konih/atmosmesh/docs/design/atmosmesh-gift.md

# AtmosMesh Gift — design and architecture proposal

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

## 1. What is being built, and the constraint that defines it

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

### The giftability contract

| # | Rule | Consequence |
| --- | --- | --- |
| G1 | The recipient never sees a terminal | Wi-Fi, location and units are set on-screen |
| G2 | No account, no API key, no subscription | Open-Meteo (keyless) for outdoor data; never OpenWeatherMap |
| G3 | It is silent | No fan. This disqualifies every PM sensor with a fan — see §5 |
| G4 | It is useful with no network at all | Onboard sensors render offline; the network adds outdoor data, clock and optional MQTT |
| G5 | It never lies about a number | An estimate may be shown, and must be labelled as one: only a real NDIR-class part may carry a bare `CO₂` label (D-002, `inventory.md:415`). A stale reading is never a zero |
| G6 | It is recoverable without tools | On-screen "forget network"; a fallback setup access point |

## 2. Reference survey

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

**Nothing from these repos gets imported.** They are read; AtmosMesh code is written.

## 3. The board, and what it actually allows

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

### Pin map (community reference — a hypothesis to verify at bring-up, not a datasheet)

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

### The free-pin budget — the single most important fact

**Three pins, one of them input-only.**

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

> **Every sensor on this product must be I²C, and they all share one bus on CN1.**

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

### Power

The CYD's 3.3 V LDO has little headroom once the panel and backlight are lit (`inventory.md:584`),
so the sensor choice in §5 is partly a power decision. **With the chosen set — ENS160 + AHT20 and
BME280 — this is not expected to be a problem:** the BME280 is a microamp part, and while the
ENS160 drives a metal-oxide hotplate and is therefore not one, it is nowhere near the 205 mA pulse
of the CO₂ sensor this design rejected. **Take the ENS160's actual figure from its datasheet and
then measure it at GF-02** — this repo does not take heater currents from memory
(`inventory.md:415`), and "not expected to be a problem" is a hypothesis until the rail is watched.

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

### Errata to design around

- **Display controller unknown.** `2432S028` ships with ILI9341 *or* ST7789, differing in colour
  inversion and RGB/BGR order. The community heuristic is that **dual-USB boards (Micro-B + Type-C)
  are the ST7789 "CYD2USB" variant with inverted colours** — and the inventory records the operator's
  units as having *both* connectors (`inventory.md:567`). **Working hypothesis: these are ST7789,
  colour-inverted.** Unverified. §6 makes this a runtime concern rather than a rebuild.
- **Never connect both USB ports at once** — one bridge, two sockets.
- Some Type-C sockets on this board lack CC resistors and will not enumerate with a C-to-C cable.
- Touch shares no bus with the TFT; use the bit-banged XPT2046 driver to avoid contention.
- **4 MB flash.** An Arduino + LVGL + Wi-Fi image is comfortably under 2 MB, so a dual-OTA partition
  layout fits — but only just, and it must be decided before the first flash, not after.

## 4. Honest objections to the premise

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

## 5. Sensors

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

### The build — €0, both parts already free in the drawer

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

**Two things about the ENS160 that must be handled, not assumed:**

- **It needs warm-up.** ScioSense state roughly **3 minutes** before readings are meaningful, plus
  a longer first-use conditioning period. That is precisely what §8's `WARMING_UP` state exists
  for: on a gift's first power-on the screen must say "Warming up…" and show `"--"`, not a wrong
  number that later moves. Take the exact conditioning figure from the datasheet at GF-02 — this
  repo does not take heater or warm-up numbers from memory (`inventory.md:415`).
- **Its current is a hotplate current, not a microamp one.** It will not trouble the 3.3 V rail the
  way the SCD41's 205 mA pulse would, but the figure goes in `inventory.md` measured, not guessed.
  The module carries a regulator for the ENS160's 1.8 V core; **feed it 3V3** until that regulator
  and the board's pull-ups have been inspected.

### The eCO₂ register: displayed, but never labelled bare "CO₂"

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

**Why that is good enough here.** In a home the dominant source of both VOC bio-effluents and CO₂
is the same thing — people. They co-vary, which is why ScioSense's own Figure 3 shows `eCO₂`
tracking a reference NDIR sensor closely across two meeting sessions, and why their Figure 4 argues
`eCO₂` is *better* than NDIR in a bedroom or bathroom, because it also catches odours and
bio-effluents a pure CO₂ sensor is blind to. Driving a ventilation prompt from it is the sensor's
designed purpose, not an abuse of it. **So the Gift shows a stuffiness reading and does say "open a
window."**

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

That second case is why the **label** matters even though the **signal** is useful.

### The one hard rule on this part

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

**`gift_view_model` carries the host test** — asserting that the eCO₂ value always reaches the UI
and MQTT through its estimated-label path, and that no code path emits it under a bare CO₂ name or
entity id. The test now guards the label rather than suppressing the value.

### Still free in stock, if a later revision wants better

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

### If CO₂ is wanted after all, the cheap way in

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

### Deliberately excluded, with reasons

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

### If particulates are non-negotiable

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

## 6. Firmware architecture

AtmosMesh Gift becomes a fourth product under ADR-0001's existing four-layer scheme — one
PlatformIO project, one explicit composition root, shared host-tested domain code.

```text
firmware/
  include/atmosmesh/
    gift_pins.hpp            CYD pin map + CN1 I2C assignment, one place
    gift_profile.hpp         ProductProfile entry: atmosmesh-gift-v1
    air_band.hpp             TVOC / AQI -> named band + verdict wording [host-tested]
    reading_state.hpp        WARMING_UP | OK | STALE | FAULT            [host-tested]
    wifi_credentials.hpp     SSID/PSK validation, NVS record shape      [host-tested]
    provisioning.hpp         the provisioning state machine             [host-tested]
    gift_view_model.hpp      every string the UI draws, incl. "--"      [host-tested]
    gift_openmeteo.hpp       JSON -> outdoor reading struct             [host-tested]
    gift_mqtt_contract.hpp   GiftMqttState, extends the D-007 contract  [host-tested]
  src/
    air_band.cpp  reading_state.cpp  wifi_credentials.cpp
    provisioning.cpp  gift_view_model.cpp  gift_openmeteo.cpp     <- native env
    gift_display.cpp      LovyanGFX panel + LVGL bind      \
    gift_touch.cpp        XPT2046, bit-banged               |
    gift_sensors.cpp      ENS160+AHT20 + BME280, one bus   |  device only,
    gift_nvs_store.cpp    Preferences/NVS                   |  excluded from
    gift_net.cpp          Wi-Fi + NTP + Open-Meteo client   |  the native env
    gift_ui_*.cpp         one file per screen              /
    products/atmosmesh_gift_v1.cpp   the composition root
```

**The rule that makes this testable:** anything that decides *what* to show is a pure function in
the native env with Unity tests written first (AGENTS.md workflow step 3, GUIDELINES §A3). Anything
that touches a pin or a socket is a thin device-only file with no logic in it. `gift_view_model`
is the seam — it turns readings and state into the exact strings and colour-band enums the LVGL
layer paints, so the screen's behaviour on a dead sensor is a host test, not a bench observation.

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

**MQTT stays exactly as D-007 and D-019 define it,** and ships **disabled**. A gift recipient with
no broker must never see an error about one. Settings gains an "Advanced → Home Assistant" panel
that, when filled in, brings up the existing `mqtt_session` machinery with a `GiftMqttState` built
from the same `MqttReading{value, valid, age_ms}` shape the other products use — so a stopped
sensor reaches Home Assistant as *unavailable*, never as clean air.

## 7. Wi-Fi provisioning

Structurally Heftie's, with its two weaknesses fixed and one thing neither reference does.

```text
         ┌──────────────┐
  boot ─►│  LOAD_CREDS  │
         └──────┬───────┘
         none   │   found
      ┌─────────┴─────────┐
      ▼                   ▼
┌───────────┐      ┌─────────────┐  ok   ┌────────┐
│  WIZARD   │      │ CONNECTING  ├──────►│ ONLINE │
│ scan list │      └──────┬──────┘       └───┬────┘
│  keyboard │   timeout/  │                  │ link lost
└─────┬─────┘   auth fail │                  ▼
      │                   ▼            ┌───────────┐
      │            ┌─────────────┐     │ RETRYING  │
      │            │   FAILED    │     │ backoff   │
      │            │ reason shown│     └───────────┘
      │            └──────┬──────┘
      │                   │ 3 failures, or user taps "Set up with my phone"
      ▼                   ▼
   ┌────────────────────────────────┐
   │ SETUP_AP  SoftAP + captive     │
   │ portal + join QR on the screen │
   └────────────────────────────────┘
```

Decisions inside it:

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

## 8. The interface

240×320 panel, **landscape 320×240** on a stand. Designed for *pressed taps on large targets*,
because §4.2 says the touch is resistive.

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

```text
┌────────────────────────────────────────────┐
│  Living room            ⌂ 21:04    [ wifi ]│
│                                            │
│        ╭──────────╮                        │
│        │  Stuffy  │      21.4 °C           │
│        │          │      47 % RH           │
│        ╰──────────╯                        │
│        Air quality      eCO₂ ~1240 est.    │
│                         TVOC  340 ppb      │
│      Open a window                         │
├────────────────────────────────────────────┤
│   Now  │  Trend  │  Outside  │  Settings   │
└────────────────────────────────────────────┘
```

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

**States are part of the design, not an afterthought (G5):**

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

## 9. Open decisions for the operator

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

1. **Product name.** `Gift` fits the existing one-word-noun family (Room, Spot, Aqua, Grove) and
   states the intent. Alternatives: `Glass`, `Desk`, `Cube`. *Recommended: Gift.*
2. ~~**Sensor tier.**~~ **Answered 2026-09-20 → D-036: ENS160 + AHT20 for gas, BME280 for
   climate, SHT41 kept as the fleet spare, no CO₂ sensor.** See §5. The MH-Z19C upgrade path stays
   open and GPIO35 is reserved for it.
3. **Which CYD.** Use an on-hand `R` (resistive, stylus) unit, or buy a `C` (capacitive) unit for
   the gift and keep the `R` pair for bench work. *Recommended: buy a `C` — see §4.2.*
4. **Graphics stack.** LVGL 9 + LovyanGFX with runtime panel detection, or LVGL 8 + TFT_eSPI to
   stay closer to nicholaswilde's copyable UI code. *Recommended: LVGL 9 + LovyanGFX — see §6.*
5. **Does MQTT ship enabled?** *Recommended: no — off by default, enabled in Settings.*
6. **Enclosure.** Not cosmetic: §4.1 makes sensor placement a measurement decision. A printed case
   that holds the sensors on the pigtail away from the board, with its own vents, or no case.
7. **OTA.** A dual-OTA partition layout on 4 MB must be chosen before the first flash. Worth it for
   a device that leaves the house; costs the option of a single large app partition.

## 10. Proposed story sequence

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

| Story | Outcome | Gate |
| --- | --- | --- |
| GF-01 | CYD unit identified from its own silicon: display controller, touch controller, board suffix, RGB LED and LDR exercised | A self-test image reports every device over serial and on screen |
| GF-02 | CN1 I²C bus proven with one sensor, pull-ups measured, 3.3 V rail watched under load | Meter (or scope) evidence on the rail; `inventory.md` updated with measured facts, replacing the community pin map with probed ones |
| GF-03 | Host-tested domain: `air_band`, `reading_state`, `wifi_credentials`, `provisioning`, `gift_view_model` | `task test` green, tests written first |
| GF-04 | LVGL 9 + LovyanGFX bring-up with runtime panel detection; the Now screen renders from fake readings | Both on-hand units render correctly from one image |
| GF-05 | Provisioning end to end: wizard, keyboard, test-before-save, inline failure, SetupAP + join QR, forget | A factory-reset unit joins a network with no serial cable touched |
| GF-06 | ENS160+AHT20 and BME280 live, four reading states visible on demand, `eCO2` shown as an estimate | Sensor unplugged mid-run shows FAULT not a frozen number; a host test proves every `eCO2` path carries the estimated label and none emits a bare `co2` name or entity id |
| GF-07 | Open-Meteo: geocoding search, forecast, outdoor AQI, NTP clock | Works with no account and no key |
| GF-08 | Optional MQTT + Home Assistant discovery, off by default | Existing D-007 contract unchanged |
| GF-09 | Enclosure, self-heating measured against a reference thermometer, offset documented or designed out | §4.1 closed with numbers |
| GF-10 | 48-hour unattended run, then hand it over | Power-loss, sensor-loss and network-loss behaviour all observed |
