konih/atmosmesh/agent-context/stories/SP-01.md

# SP-01 — AtmosMesh Spot: a 3.3 V presence-and-climate node on an ESP32-C3 SuperMini

- **Status:** Proposed (design spec; carrier soldering started 4 September 2026)
- **Priority:** P3 — small, self-contained, and the ESP32-C3 toolchain spike R2-01 needs anyway
- **Milestone:** Spot v1
- **Depends on:** nothing open. SuperMini pin map and OLED bus pins are photo- and
  scan-verified, the LD2410S datasheet is read, the SHT41 and VEML7700 breakouts are photographed
  (see Evidence).
- **First unit:** SHT41 + VEML7700 + HLK-LD2410S on the board and the DS18B20 probe on a
  terminal. **No BME280** (operator decision, 5 September 2026; the outdoor-cable variant that
  existed on 4 September is withdrawn). Drawings and bill of materials in
  [`hardware/kicad/atmosmesh-spot/wiring.md`](../../hardware/kicad/atmosmesh-spot/wiring.md).

## User story

As the operator, I want a palm-sized station that I can build in an evening, put in any room that
has a USB socket, and read on its own little screen or in Home Assistant, so that the rooms without
a Room-class station get temperature, humidity, light and — the thing PIR never gave me — whether
somebody is actually in the room; and I want a temperature probe on a lead so the same node can
watch a radiator, a window pane or the air outside a window without any electronics leaving the
room.

## Outcome

One carrier on a 14 × 20 hole perfboard, one population:

| Product id | On the board | On a terminal | Bus |
| --- | --- | --- | --- |
| `atmosmesh-spot` | SuperMini, SHT41 at `0x44`, VEML7700 at `0x10`, HLK-LD2410S radar | DS18B20 probe, 2.5 m, 1-Wire | one 3.3 V I²C bus at 100 kHz, OLED at `0x3C` |

Everything is one 3.3 V domain. Firmware is one product built with a PlatformIO `esp32-c3`
environment, publishing on the existing MQTT contract, with the on-board 72 × 40 OLED cycling
through the values.

**The first unit takes the last SHT41 spare and the only LD2410S.** After Room, Room v2 and
this unit, one SHT41 and one VEML7700 remain; a second Spot needs another SHT41 bought and a
second radar, or goes without presence. The six BME280 in stock stay unassigned.

## Sensor choices, and why

- **SHT41 for temperature and humidity.** The accurate one (about ±1.8 %RH, ±0.2 °C), and the
  last free spare.
- **No BME280.** Decided against on 5 September. It would have brought pressure and, on a cable,
  an outdoor reading; the operator prefers a simpler board without the cable, its series
  resistors, its clamps and its terminal. Pressure is not a Spot value; an outdoor temperature,
  if wanted, comes from the DS18B20 probe held out of the window.
- **VEML7700** for lux, as on Room. Mounted on its header facing the room, on the side away from
  the OLED so the display's own glow does not become the reading.
- **HLK-LD2410S** for presence. It is the 3.3 V, low-power member of the LD24xx family with a
  presence output pin and a UART, which is exactly what a board without a 5 V domain needs.
  There is one, and it was reserved for Room v2; Room v2 has a 5 V domain and takes the LD2450
  instead (R2-01 updated). The manual (read 4 September, filed under
  `docs/hardware/datasheets/`) settles it: 3.0–3.6 V supply, every pin 0–3.3 V, average current
  under 1 mA with transmit peaks near 118 mA, presence on pin `OT2` (high = occupied), UART on
  `OT1` (TX) and `RX` at 115200 8N1.
- **DS18B20 probe** because 1-Wire is built for a lead and the probe is already encapsulated.
  It is the only thing that may leave the room.
- **Not potted, not outside.** Coating the ceramic antenna detunes the SuperMini's weakest part.
- **Soil header dropped.** Three sensors and a radar fill the small board; a plant node is a
  different population and can be a later story.

## Controller: ESP32-C3 SuperMini OLED — verified

- 3.3 V logic and a small on-board LDO from USB 5 V. **The `5V` pin is never wired to anything on
  the carrier.**
- OLED: SSD1306 driving a 72 × 40 panel with a column offset; some libraries name the same panel
  "70 × 42". **Scanned 4 September: `0x3C` on SDA = GPIO5, SCL = GPIO6**, nothing else on the bus
  of the bare module. Whether the OLED has its own pull-ups is a meter reading still to take.
- Strapping pins **GPIO2, GPIO8, GPIO9** stay unused as inputs. GPIO8 drives the on-board LED,
  GPIO9 is the BOOT button — the display page button in firmware, nothing on the carrier.
- **Pin map, photo-verified 4 September** (USB on the left, OLED up). Row A, the side with the
  `PWR` and `IO8` LEDs, from the USB end: `5V GD 3V RX TX 2 1 0`. Row B, from the USB end:
  `10 9 8 7 6 5 4 3`. `RX`/`TX` are GPIO20/21. This is not the plain SuperMini's map.
- GPIO assignment: GPIO5/6 I²C (row B); **GPIO3** radar `OT2` (presence, row B far end);
  the board's marked **`RX` (GPIO20)** ← radar `OT1` (its TX) and **`TX` (GPIO21)** → radar
  `RX`, i.e. UART0, `Serial0` in the Arduino core (row A); **GPIO4** 1-Wire (row B). GPIO0 and
  GPIO1, two of the five ADC pins, stay free. Changed 5 September on the operator's question:
  the earlier choice of GPIO0/1 as a second UART avoided the ROM boot log that the C3 prints on
  `TX` at every reset, but that log cannot form a radar command (header `FD FC FB FA` plus a
  valid length), the USB console is native USB on this board so UART0 is otherwise unused, and
  the labelled pins are the ones a builder reaches for.
- Known SuperMini trait: the ceramic antenna couples badly and Wi-Fi drops at full TX power.
  Firmware limits TX power to about 8.5 dBm at start-up as part of the product.
- Pin rows: 8 pins each, **7 pitches (17.78 mm) apart — dry-fit confirmed by the operator on
  4 September**: pushed into the 14 × 20 board the module fits with three free columns on each
  side, i.e. rows at columns 4 and 11.
- Chip on the first unit: ESP32-C3 rev 4, 4 MB flash, MAC `E4:EC:E6:92:05:D4`.

## Sensor set, bus map and headers

| Device | Address / pin | Header | Notes |
| --- | --- | --- | --- |
| SHT41 | `0x44` | `J_SHT` 4-pin: VIN, GND, SCL, SDA | Photo-confirmed order. The `SHT4X` board carries a 662K LDO, a level shifter and a fitted `103` array on the sensor side; its host-side pull-up pads are empty, so it adds **no** pull-up to the bus |
| VEML7700 | `0x10` | `J_VEML` 5-pin: VIN, 3VO (NC), GND, SCL, SDA | Photo-confirmed order (`HW-900`); same LDO-plus-shifter architecture with all four array elements in use, so about 10 kΩ per line; `3VO` never wired |
| HLK-LD2410S | `OT2` → GPIO3, `OT1` → `RX` (GPIO20), `RX` ← `TX` (GPIO21) | `J_RAD` 5-pin in the manual's J2 order: **3V3, GND, OT1, RX, OT2** | Datasheet- and photo-confirmed 3.3 V part. `OT2` is the presence output (high = occupied), direct to GPIO3. `OT1` is the UART **TX** despite the name. `C_RAD_BULK` 100 µF at the header for the ~118 mA transmit peaks |
| OLED on the SuperMini | `0x3C` | on board | Scan-confirmed on GPIO5/6 |
| DS18B20 probe | 1-Wire, GPIO4 | `J_1W` 3-pole terminal: 3V3, DQ, GND with `R_1W` 4.7 kΩ to 3V3 | Surface, water or outside-the-window temperature on the 2.5 m lead |

No address collides. Carrier pull-ups `R_PU_SDA`/`R_PU_SCL` are **4.7 kΩ**; with the VEML7700's
10 kΩ the line sees about 3.2 kΩ, with an assumed 10 kΩ on the OLED about 2.4 kΩ — 1.4 mA sink,
well inside the 3 mA limit. Bus speed 100 kHz; the bus never leaves the board.

Radar placement rules, from Room v2's lesson in reverse: the antenna face looks into the room
with no metal or copper in front of it, the module stands on its header at the board edge, and it
must not look across a fan, a curtain in a draught or a pet's bed — a 24 GHz radar reports every
one of those as a moving target. Presence is confirmed with a person sitting still and with the
room empty before it drives anything.

## Board layout — 14 × 20 holes (35.6 × 50.8 mm)

Columns 1–14 left to right, rows 1–20 top to bottom, viewed from the component side, USB
overhanging the row-1 edge. The 10 × 24 board does not fit: with the rows 7 pitches apart the
module needs 8 of the 10 columns and leaves no keep-out beside the antenna end.

**The authoritative hole-by-hole drawing is in
[`hardware/kicad/atmosmesh-spot/wiring.md`](../../hardware/kicad/atmosmesh-spot/wiring.md)
(section 3) and its SVGs.** In outline:

| Rows | Contents |
| --- | --- |
| 3–10 | `U1` socket rows at columns 4 (row A: `5V GD 3V RX TX 2 1 0`) and 11 (row B: `10 9 8 7 6 5 4 3`), 7 pitches apart |
| 9–13 | keep-out around the module's far end: buttons and antenna. No copper, no wire, no coating |
| 14 | `R_PU_SDA`, `R_PU_SCL` 4.7 kΩ, `C1` |
| 15 | `J_SHT` (cols 1–4), `J_VEML` (cols 7–11), both modules standing upright |
| 16–18 | decoupling, test points, `R_1W`, `C_RAD_BULK`/`C_RAD` |
| 20 | `J_RAD` (cols 1–5, radar upright, face outward), `J_1W` terminal (cols 8/10/12) |

`J_VEML` and `J_RAD` sit on different edges so the light sensor can face one way and the radar
the other; on a windowsill unit the radar faces the room and the VEML7700 faces up.

Wiring by pin name, all on one 3.3 V rail:

```text
U1 3V3 ──┬── J_SHT VIN  ──┤C_SHT 100n── GND
         ├── J_VEML VIN ──┤C_VEML 100n── GND          J_VEML 3VO: not connected
         ├── J_RAD 3V3  ──┬┤C_RAD_BULK 100µ (+)── GND
         │                └┤C_RAD 100n── GND
         ├── J_1W 3V3 ── R_1W 4k7 ── J_1W DQ ── U1 GPIO4
         ├── C1 100n ── GND
         └── R_PU_SDA 4k7 ── SDA      R_PU_SCL 4k7 ── SCL

U1 GPIO5 (SDA) ── SDA ── J_SHT SDA ── J_VEML SDA
U1 GPIO6 (SCL) ── SCL ── J_SHT SCL ── J_VEML SCL
J_RAD OT2 ── U1 GPIO3           presence, high = occupied, 3.3 V logic, direct
J_RAD OT1 ── U1 RX (GPIO20)     radar UART TX → frames in (C3 UART0 RX, Serial0)
J_RAD RX  ── U1 TX (GPIO21)     configuration out (C3 UART0 TX)
U1 GND ── ground rail ── every GND
U1 5V  ── nothing
```

## Power

USB only. The SHT41 and VEML7700 draw about a milliampere each, the OLED a few. The radar's
transmit bursts are why `C_RAD_BULK` sits at its header. The other real load is the C3's Wi-Fi
transmit burst (up to ~350 mA) on the SuperMini's small LDO, which is why the TX-power limit
matters for supply as well as for range. If the board browns out on connect, add 10 µF at
`TP_3V3` and record it.

## Firmware

**Built and flashed 5 September 2026 — see [SP-02](SP-02.md) for the image and its evidence.**

- Composition root `firmware/src/products/atmosmesh_spot_v1.cpp` per ADR-0001, PlatformIO
  environment `atmosmesh-spot-v1` for the C3 (USB CDC on boot). The product repeats the hello
  with its name and station id.
- Reuses the I²C scan-and-report behaviour and the MQTT contract shape (`{value, unit, valid,
  age_ms}`). Station id `atmosmesh-spot-0001`, following the product pattern already in use
  (`atmosmesh-room-0001`), one per unit.
- Entities: `temperature_c`, `humidity_pct` (SHT41), `illuminance_lx`, `presence` (radar `OT2`
  through a debounce and hold), `probe_temperature_c` (DS18B20, unavailable when no probe
  answers), `presence_distance_cm` and `presence_state` from the LD2410S UART (minimal frame
  `6E · state · distance · 62`, standard frame also decoded), `wifi_rssi_dbm`. The product works
  on `OT2` alone; the UART entities stay unavailable until frames arrive.
- OLED: one value per page, rotated every 3 s, the BOOT button forces the next one; a presence
  glyph top-right and the link state bottom-right on every page.
- Bus speed 100 kHz. Wi-Fi TX power limited to 8.5 dBm at start-up; RSSI in every 5 s log line
  and published.

## In scope

- One carrier; the first build goes on the bench next to Room for the comparison criteria.
- PlatformIO C3 product environment, host-tested Sensirion CRC, MQTT discovery for the new
  product, 1-Wire probe reading.

## Out of scope

- Battery operation. The SuperMini has no charger, and deep-sleep with an OLED and a radar is a
  different product.
- Any electronics outside besides the probe. Coating or potting the node is rejected above.
- A BME280, on the board or on a cable (withdrawn 5 September).
- The ESP32-C6 modules. Same spike, different chip; after the C3 works.
- Any 5 V sensor, including the LD2450. The board has no 5 V domain by design.
- Radar zones, distance thresholds and multi-target anything.

## Acceptance criteria

- [x] Given the PlatformIO C3 environment, when a firmware builds and flashes, then the serial
      log shows a hello and a bus scan on real hardware. **Met on 4 September by
      `firmware/tools/c3scan`** and on 5 September by the product image itself
      (`spot: boot product=atmosmesh-spot-v1 station=atmosmesh-spot-0001 …`, SP-02).
- [x] Given the SuperMini photographed and scanned, when the OLED pins and the breakout pull-ups
      are recorded in `docs/hardware/inventory.md`, then the carrier's `R_PU_*` value is written
      down. **4.7 kΩ**; only the OLED's own pull-up is still a meter reading.
- [x] Given the LD2410S datasheet, when supply voltage, current and output level are recorded,
      then the radar header is either approved for 3.3 V or the radar is struck from this story.
      **Approved:** 3.0–3.6 V, all pins 0–3.3 V (`docs/hardware/datasheets/README.md`).
- [x] Given the bus scanned with only the OLED fitted, then exactly `0x3C` answers; with the
      sensors fitted, `0x44` and `0x10` join it and nothing else. **Bare module 4 September:
      `0x3C` only. Soldered carrier 5 September: `0x10 0x3C 0x44`, nothing else.**
- [ ] Given the node beside Room's SHT41 for one hour, when the readings are compared, then
      temperature agrees within 0.5 °C and humidity within 3 %RH, or the difference is explained.
- [ ] Given a person sitting still for 5 minutes, then `presence` stays `on`; given the room
      empty for 5 minutes with any fan or curtain in the radar's view noted, it is `off`.
- [ ] Given the probe rung out and connected, then `temperature_probe` tracks a hand and agrees
      with the SHT41 within 1 °C in still room air.
- [ ] Given Wi-Fi at limited TX power, when the node runs for 24 hours, then no reconnect gap
      longer than 5 minutes appears in the log.
- [ ] Given the probe unplugged at runtime, then the other entities keep updating and
      `temperature_probe` reports unavailable within one publish interval.

## Validation

- Automated: Sensirion CRC against datasheet examples; MQTT payload schema; unavailable-device
  behaviour for each sensor independently; presence hold-time logic.
- Manual: bus scans per stage, radar `OT2` idle and active levels with the meter before GPIO3 is
  connected, side-by-side comparison with Room, presence still-sitting and empty-room tests,
  RSSI log.
- Failure/edge case: any breakout unplugged at runtime; USB power cycled (reconnects without
  manual reset); radar `OT2` stuck high; probe lead shorted DQ to GND (the 4.7 kΩ limits it and
  the bus recovers when the short clears).

## Evidence

- 2026-09-04 — HLK-LD2410S user manual V1.3 and serial protocol V1.00 retrieved from Hi-Link's
  official Drive folder into `docs/hardware/datasheets/` (SHA-256 in that README). Table 3-2:
  J2 = `3V3` (3.0–3.6 V), `GND`, `OT1` UART_TX, `RX` UART_RX, `OT2` presence IO, all 0–3.3 V.
  Table 2-1: average current 0.04–0.6 mA; page-4 tool screenshots show peaks near 118 mA.
  Protocol section 2: 115200 8N1, minimal frame `6E · state · distance(2) · 62`.
- 2026-09-04 — operator read the breakouts: VEML7700 carries a `103` part, SHT41 has an empty
  `103` footprint. Meter confirmation of ~10 kΩ from SDA and SCL to VIN on the VEML7700 still to do.
- 2026-09-04 22:42–22:44 — nine photos (SuperMini on the perfboard, SHT41 front/back, LD2410S
  front/back, VEML7700 front/back, BME280 front/back), evaluated and deleted afterwards at the
  operator's request. Facts recorded in `docs/hardware/inventory.md`: SuperMini pin map (row A
  `5V GD 3V RX TX 2 1 0`, row B `10 9 8 7 6 5 4 3`, from the USB end); SHT41 `VIN GND SCL SDA`
  with a `662K` LDO, a level shifter, a fitted `103` array and two empty host-side pull-up pads;
  VEML7700 `HW-900` `VIN 3VO GND SCL SDA` with the same architecture and a fitted `103` array;
  BME280 `GY-BM E/P 280` 6-pin, no regulator, four 10 kΩ, SDO low (recorded as stock knowledge;
  the part is no longer in this design); LD2410S silkscreen `3V3 GND OT1 RX OT2` matching the
  manual. The perfboard photo was the module **pushed into the board**: it fits with three free
  columns on each side, so the rows are 7 pitches apart.
- 2026-09-04 — **first ESP32-C3 build in this repository succeeds:** `firmware/tools/c3scan`
  (PlatformIO `espressif32` 7.1.0, Arduino core 3.20017, RISC-V toolchain 8.4.0) builds the I²C
  pin-pair scanner: RAM 4.3 %, flash 19.9 % of 1.3 MB. Two PlatformIO gotchas are recorded in
  the tool's README.
- 2026-09-04 23:15 — **scanner flashed and run** (after `usermod -aG dialout` and opening the
  port for the session): chip ESP32-C3 rev 4, 1 core, 4 MB flash, MAC `E4:EC:E6:92:05:D4`.
  Scan: `SDA=GPIO5 SCL=GPIO6 -> device at 0x3C`, every other pair empty.
- 2026-09-05 — **operator decision: no BME280.** The In/Out variant with the outdoor cable, its
  4-pole terminal, 100 Ω series resistors, four 1N5819 clamps and 2.2 kΩ pull-ups is withdrawn;
  the carrier pull-ups return to 4.7 kΩ and the bus stays on the board. The DS18B20 probe stays.
- 2026-09-05 01:15 — **carrier soldered and tested by the operator.** `c3scan` on the finished
  board: `SDA=GPIO5 SCL=GPIO6 -> 0x10 (VEML7700), 0x3C (OLED), 0x44 (SHT4x)`, every other pin
  pair empty.
- 2026-09-05 01:30–02:00 — **product image `atmosmesh-spot-v1` flashed** (SP-02). Every sensor
  reads, presence follows `OT2`, Wi-Fi associates with the TX limit applied, the broker accepts
  `atmosmesh-spot-0001`. First image hung in the OLED init (U8g2 given pin numbers on Arduino
  core 3.x; fixed, see SP-02). The SHT41 reads ~3 K above the DS18B20 probe and climbs while the
  board warms — self-heating to be explained before the Room comparison.
- 2026-09-05 01:50–02:10 — **radar UART line open.** `OT2` works, but GPIO20 sees nothing: it
  idles LOW against a pull-down and HIGH against a pull-up (floating), 0 bytes in 40 s, and a
  pin-edge probe over every free GPIO (0, 1, 2, 7, 10, 20, 21) found no edges in 16 s and no
  ACK to an enable-config/read-version command on either pin polarity. Operator confirms the
  wiring: GPIO20 (RX) to `OT1`, GPIO21 (TX) to the radar `RX`, nothing in series. So the fault
  is on the `OT1` path itself — a joint at either end, or the module's own header pin. Meter
  checks: continuity radar `OT1` pin ↔ SuperMini `RX`; ~3.3 V on the radar's `OT1` pin against
  GND while powered. Firmware needs no change once the line conducts.
- 2026-09-05 02:20 — **scope and Operation Guide.** Operator's scope: the radar's `OT1` shows
  nothing, only the SuperMini's `TX` idles high. Hi-Link's Operation Guide 1.0 (now in
  `docs/hardware/datasheets/`) says the module reports continuously by default, answers the
  enable-configuration command when healthy, and has no low-power or jumper setting. Its wiring
  photo shows the pads the operator noticed: three link footprints between the chip and the
  `RX`/`OT1` header pins, top and bottom fitted, middle empty on the working reference unit.
  Next: meter which footprint belongs to `OT1` and whether its link conducts; bridge it if not.
- 2026-09-05 02:40–03:30 — **radar UART working.** The operator reflowed the module's chip (no
  direct trace from `OT1` could be found). After that, four stacked causes, each found after the
  previous one was fixed (details and captures in SP-02): (1) the reflow itself — the module now
  sent its enable-config ACK at every C3 reset, proof of a working transmitter; (2) the firmware's
  wiring check had left the C3's internal pull-down on GPIO20, and `OT1` is a weak driver that
  follows the pull — with a pull-up the frames decode; (3) after a reset the module sends two or
  three frames and waits until it sees a break on its RX, so the firmware sends one at boot;
  (4) IDF log output on UART0 fed the module's parser, now silenced. End state: `<- ack end-config
  status=0`, continuous minimal frames at 3–4 Hz, `presence_distance_cm` and `presence_state`
  valid. Also fixed on the way: the VEML7700 auto-range read took 5.1 s in the dark.
- 2026-09-05 03:20 — after the operator announced leaving the room, the radar kept reporting
  state 2 at ~71 cm for the whole 2.5 min capture (brief readings at 350 and 165 cm at the start).
  Either the operator was still within view or a fixed reflection ~0.7 m in front of the module
  passes the default gate-1 threshold. Empty-room test pending; threshold auto-generation
  (protocol command `0x0009`, room empty) is the tool if it is the latter.

## Open questions

1. ~~Which GPIOs carry the OLED?~~ Closed by scan: `0x3C` on SDA = GPIO5, SCL = GPIO6. Whether
   the OLED carries pull-ups is still a meter reading (SDA to 3V, unpowered).
2. ~~Are the pin rows 7 pitches apart?~~ Closed by the operator's dry-fit.
3. ~~LD2410S: supply range, current, output level and polarity, UART baud rate.~~ Closed, see
   Evidence. Only its header pitch remains to be measured on the part.
4. ~~BME280 breakout.~~ Moot: the BME280 is out of the design (5 September).
5. ~~Screw-terminal pitch for `J_1W`: 5.08 mm assumed, measure before soldering.~~ Soldered;
   the probe is found and reads.
6. ~~Why does nothing arrive on the radar `OT1` → `RX` line?~~ Closed 5 September: an open
   joint fixed by reflow, then a pull-down left on the C3's RX pin, a break the module needs
   before it streams, and IDF log noise on the line. For the next unit consider `R_RAD_PU`
   10 kΩ from `OT1` to 3V3 on the carrier so the weak driver does not rely on the C3's pull-up.
7. SHT41 self-heating on the carrier: ~3 K above the probe after minutes. Compare against Room
   before deciding whether the sensor wants a lead or a cut-out.
8. Is the ~71 cm "somebody" with the room empty a real reflection? If so, run the radar's
   threshold auto-generation with the room empty (SP-04).

## Follow-on stories

SP-02 C3 product environment and composition root · SP-03 carrier bring-up and comparison
against Room · SP-04 LD2410S UART frames · SP-05 further units and per-room discovery.
