konih/atmosmesh/agent-context/handoffs/2026-08-24-atmosmesh-grove-v1.5.md

# AtmosMesh Grove v1.5 software handoff — 2026-08-24

## Completed

- V15-01 hardware/identity contract and V15-02 shared variant architecture.
- Accepted ADR-0001, two-product matrix, named composition roots and canonical/compatibility builds.
- Native-tested profile and explicit health/display formatting.
- Compiling ESP8266 Grove image plus preserved ESP32 build and task commands.
- Product, wiring, GPIO0 boot caveat and deferred analog constraints reconciled across docs.

## Hardware result

The coordinator flashed reviewed head `a681990` under explicit authorization. Boot identity and
the D2/D3 bus matched the Grove profile. BMP180 passed five stable samples. OLED initialization at
0x3C passed, but pixels are not visually confirmed. DHT11 on profile D5/GPIO14 failed every read.
The captured banner reported product name, variant and station ID but not a separate stable product
ID. After independent approval of final head `50ca2f3`, a second authorized flash wrote 287,952
verified bytes and captured the corrected identity contract exactly:

```text
product=AtmosMesh Grove product_id=atmosmesh-grove-v1.5 variant=atmosmesh-v1.5 station_id=atmosmesh-grove-0001
```

OLED initialization again passed but pixels remain visually unconfirmed. BMP180 passed four more
samples at 24.6–24.7 °C / 984.3 hPa. DHT11 was initially unavailable, then a later run produced
32.0→31.0 °C / 32% RH on D5/GPIO14 while BMP180 reported 25.6 °C / 983.9–984.0 hPa. Treat this as
communication evidence, not DHT accuracy/calibration. AtmosMesh v1 and the ESP32 were untouched.

## Next validation

V15-04/V15-05 add the installed D7/GPIO13 bare-LDR RC response and Grove MQTT contract. The product
diff was independently approved at `e5d83e1` and CI is green. During the authorized follow-up,
secret generation and the firmware build succeeded, but `/dev/cu.usbserial-0001` disappeared before
esptool opened it. Upload failed with `FileNotFoundError` before connecting or writing, so the Grove
still runs its prior firmware and no bytes from `e5d83e1` reached the device. `ls /dev/cu.*` showed
no USB serial device and ioreg showed hubs only; do not infer a firmware or board failure from this.

Reconnect/power the USB serial device and confirm its port, then validate raw light timing across
bright/dark conditions, timeout behavior, the four-line OLED page, Wi-Fi/broker-loss recovery,
retained availability and the Grove Home Assistant entities. Prior DHT11 communication evidence on
D5/GPIO14 remains valid, but is not an accuracy claim. MAX4466 is dropped.

The USB serial device later reappeared. V15-06 adds the already-installed bi-color LED on
red=D6/GPIO12 and green=D0/GPIO16, plus a cooperative YL-38 raw ADC policy using an active-low
D1/GPIO5 high-side control. The operator then confirmed and physically wired a 2N3906 PNP:
emitter=3V3, collector=YL-38 VCC, base through 2.2 kΩ to D1, and 100 kΩ base-emitter pull-up. AO is
wired through 47 kΩ / 15 kΩ to A0 with `104` decoupling; DO is unused. Software must receive fresh
independent review before the coordinator flashes it.

Independent review approved head `c880afe`, and the coordinator then flashed it successfully.
Over more than 60 seconds, serial showed two soil cycles about 30 seconds apart, each exactly
`soil: ok adc_raw=214 samples=5 power=off`; DHT11 was 25.0 °C / 36–37% RH, BMP180 was
24.4–24.5 °C / 982.6–982.8 hPa and uncalibrated light timing was 389–452 µs. This is a raw sampling
and software OFF-action pass only. LED colors/polarity, switched-rail voltage/current, physical
power-off, calibration, MQTT broker/HA receipt and OLED pixels remain pending.

V15-07 responds to the observed `L401us S214 D1B1` page. The host-tested replacement removes the
product and health-bit rows and uses four labelled lines: DHT11 temperature/humidity, BMP180
pressure, raw RC light microseconds and raw soil ADC. Serial diagnostics, the LED health policy and
the exact five-entity Grove MQTT/HA contract remain intact. Independent review approved cumulative
head `4e4a820`, which the coordinator flashed successfully. More than 30 seconds of serial showed
`mqtt: connected`, logical LED status `green/healthy`, DHT11 25.0 °C / 36% RH, BMP180
25.3–25.7 °C / 982.1–982.4 hPa, raw light 420–492 µs and raw soil ADC 214 with five samples and
software `power=off`. Broker-side receipt/HA entities, visible LED colour/polarity and visible OLED
pixels/layout were not observed and remain pending operator confirmation.

V15-08 then added the reversible full-area OLED and red/green/amber/off LED diagnostic. Operator
inspection established the fitted LED is D6 red / D0 green and common-anode: only the active-LOW
diagnostic produced the intended colors. Normal firmware was restored from merged main with an ad
hoc common-anode build flag.

V15-09 removes that footgun by making common-anode canonical while retaining a dedicated
common-cathode build. A host-tested calibration policy keeps raw soil unclassified/amber until
explicit direction and ordered raw dry/acceptable cutoffs are valid. Core/acquisition errors and
configured-offline MQTT take red priority; calibrated dry is red, needs-watering is amber, and only
calibrated acceptable plus healthy system state is green. MQTT/HA remain raw-only. All 104 native
tests and the complete product/compatibility/polarity/diagnostic build matrix pass. A later review
regression brought the suite to 105 tests by distinguishing unknown-before-first-acquisition from
a real core failure.

After independent approval of head `8fca62d`, the coordinator flashed the canonical Grove image on
2026-08-24. Esptool wrote 480,976 bytes, verified the hash and hard-reset the ESP8266EX/26 MHz
target. Serial over more than 30 seconds showed DHT11 26.0 °C / 35–37% RH, BMP180
26.1–26.3 °C / 981.5–981.6 hPa, raw light 393–401 µs and one soil cycle at ADC 213 from five
samples with software `power=off`. The resulting diagnostics reported logical common-anode amber
with both outputs LOW and `soil-calibration-needed`, calibration disabled, unknown direction and
unset thresholds. This is a runtime policy/drive-level pass, not visible LED-colour, physical
power-off or calibration evidence. Operator visual confirmation and controlled dry/wet references
remain pending.
