konih/atmosmesh/agent-context/stories/V15-08.md

# V15-08 — Grove OLED and bi-color LED visual diagnostic image

- **Status:** Blocked on independent review and operator visual inspection
- **Priority:** P1
- **Depends on:** V15-07 compiled four-row live page
- **Objective:** Provide an explicitly selected, reversible Grove image that lights the complete
  logical 128×32 framebuffer and cycles every installed bi-color LED state for operator inspection.

## Scope

- Keep the canonical AtmosMesh Grove v1.5 build in its normal four-measurement-row mode.
- Add a separately named compile-time diagnostic build that fills all 128×32 logical pixels after
  successful OLED initialization and prevents later live rendering from overwriting the fill.
- Emit an unambiguous serial startup diagnostic with the active mode and `128x32` geometry.
- While keeping the OLED filled, repeat a slow two-second-per-phase LED sequence:
  red → green → amber (both channels) → off. Use the compiled common-cathode/common-anode polarity
  through the existing status LED mapping and log every transition with D6/D0 output levels.
- Add explicit build, flash and monitor tasks so selecting the temporary image is deliberate.
- Host-test the render policy, serial banner and LED timing/polarity including `millis()` wraparound,
  then compile normal and diagnostic Grove images.

## Out of scope

- Changing AtmosMesh v1, changing Grove wiring/controller geometry, automatically flashing a
  device, interpreting physical measurements, or making the all-white screen the product default.
- Disabling sensor or MQTT runtime work while the diagnostic image holds the OLED fill and cycles
  the LED.

## Acceptance criteria

- [x] The canonical `atmosmesh-grove-v1_5` image retains normal four-row live rendering.
- [x] The explicit diagnostic image fills the entire logical 128×32 framebuffer after successful
  OLED initialization and subsequent render calls cannot overwrite it.
- [x] Serial startup states that the full-area diagnostic is active and names geometry `128x32`.
- [x] Diagnostic-only LED output repeats red → green → amber → off every two seconds, uses the
  compiled polarity, survives timer wraparound and logs each expected color plus D6/D0 levels.
- [x] The canonical Grove image retains its sensor/MQTT-driven status LED policy unchanged.
- [x] Dedicated, descriptively named build/flash/monitor tasks are documented; no flash occurs in
  this implementation lane.
- [x] Native red/green evidence and the full product gate matrix are recorded before commit.

## Validation plan

Add failing native tests for the default/diagnostic render policy and exact diagnostic banner before
production behavior. Add red tests for the four-phase LED timeline, wraparound and both polarities
before wiring the policy into the Grove loop. Build the canonical Grove environment and inspect its
compile command/default policy, then build the dedicated diagnostic environment with its explicit
flag. Run native tests, both first-class product builds, compatibility builds, repository checks
and the secret audit. A later independently reviewed operator run may leave the diagnostic running
until the operator explicitly requests restoration of the canonical Grove image.

## Evidence

- Operator requested a temporary all-pixels-on image on 2026-08-24 to measure the physical active
  area. D-017 records the reversible diagnostic boundary.
- During implementation, the operator expanded the same temporary image to exercise the installed
  bi-color LED with a visible two-second red/green/amber/off sequence and requested that it remain
  running until restoration is explicitly requested.
- **Red, 2026-08-24:** native compilation first failed because the diagnostic policy/header did not
  exist. After the LED scope was added, a second red compile failed on the absent cooperative LED
  state/begin/tick API, proving the no-skip timeline was specified before implementation.
- **Green, 2026-08-24:** 97/97 native tests pass. The canonical compiled mode is normal/live;
  diagnostic render policy holds the fill. LED tests cover two-second red/green/amber/off order,
  a late tick advancing only one phase, unsigned wraparound, all four common-cathode and
  common-anode level mappings, and transition text with actual D6/D0 levels.
- **Build selection, 2026-08-24:** PlatformIO `envdump` shows no visual-diagnostic flag in canonical
  `atmosmesh-grove-v1_5` and exactly
  `ATMOSMESH_GROVE_VISUAL_DIAGNOSTIC=1` in
  `atmosmesh-grove-v1_5-visual-diagnostic` (in addition to shared flags).
- **Full gates, 2026-08-24:** `task test`, `task build-all`, `task build`, `task build-grove`, direct
  `esp32dev` / `esp8266-grove`, canonical common-anode Grove, visual diagnostic and common-anode
  visual diagnostic builds passed. AtmosMesh v1 remained 14.6% RAM / 72.8% flash (953,625 bytes);
  canonical Grove was 42.3% RAM / 29.3% flash (306,471 bytes); the final common-anode diagnostic was
  42.3% RAM / 29.4% flash (306,575 bytes). `task check`, `git diff --check` and generated-secret
  ignored/untracked audit passed. No flash, monitor, self-review or merge occurred.
- Software acceptance is complete. Independent review and an operator-authorized flash/visual
  inspection remain pending; once flashed, the diagnostic stays installed until the operator
  explicitly requests restoration.
- **Review fix red/green, 2026-08-24:** fresh review found that the selected mode/geometry banner was
  reachable only after successful OLED initialization. A new native test failed to compile against
  the missing startup/result APIs, then passed with independent messages for selection,
  fill-applied, address-not-found and initialization-failed. Selection now prints before OLED
  probing; error paths explicitly say `fill not-applied` without weakening canonical output.
- **Review-fix gates, 2026-08-24:** 98/98 native tests and the complete prior matrix passed again:
  both canonical products, task/direct compatibility builds, canonical common-anode Grove, visual
  diagnostic and common-anode visual diagnostic. AtmosMesh v1 remained 953,625 bytes; canonical
  Grove was 34,720 bytes RAM / 306,579 bytes flash and the final common-anode diagnostic was 34,880
  bytes RAM / 306,947 bytes flash. Checks and secret audit passed. No flash, monitor, self-review or
  merge occurred.
