konih/atmosmesh/agent-context/stories/V15-09.md

# V15-09 — Grove calibrated soil-status LED

- **Status:** Blocked on controlled soil calibration and operator visual evidence
- **Priority:** P1
- **Depends on:** V15-06 raw soil acquisition and confirmed installed LED polarity
- **Objective:** Make the canonical installed LED polarity reliable and derive local red/amber/green
  status from system health plus explicitly validated, direction-aware soil calibration.

## Scope

- Make the installed D6 red / D0 green common-anode wiring the canonical Grove profile default.
- Retain an explicit, tested common-cathode build override for alternative hardware.
- Add compile-time soil calibration metadata: enabled state, raw direction, dry cutoff and
  acceptable cutoff. Support both higher-is-wetter and lower-is-wetter directions.
- Validate ADC bounds and direction-consistent strict threshold ordering. Disabled, unknown,
  out-of-range, equal or direction-reversed thresholds are uncalibrated/invalid and fail safe to
  amber, never to a guessed moisture state.
- Apply this exact LED priority:
  1. core sensor or acquisition error → red;
  2. MQTT configured but offline → red; intentionally unconfigured MQTT is neutral;
  3. calibrated soil dry → red;
  4. soil missing, uncalibrated/invalid or calibrated warning band → amber;
  5. calibrated acceptable soil with otherwise healthy system → green.
- Emit non-secret serial diagnostics with final `soil-led-status`, reason, raw state, direction and
  threshold/calibration validation state.

## Out of scope

- Inventing thresholds before operator dry/wet measurements, moisture percentage, MQTT schema or
  Home Assistant device-class changes, watering automation, OLED row changes, sampling cadence,
  switched-power changes, AtmosMesh v1 behavior, or flashing hardware.

## Acceptance criteria

- [x] Canonical Grove and visual-diagnostic images compile common-anode by default; a dedicated
  common-cathode verification image compiles and is host-tested.
- [x] Native tests cover disabled, valid-both-directions, unknown direction, out-of-range, equal and
  direction-inconsistent threshold validation.
- [x] Raw zero remains a valid soil sample; missing/unclassified is never silently converted to a
  calibrated classification.
- [x] Native tests prove the complete LED priority including MQTT configured/offline versus
  intentionally unconfigured and soil missing/acquisition failure/dry/warning/acceptable states.
- [x] Serial diagnostics expose calibration state/direction/cutoffs and final LED reason without
  credentials or moisture/percentage claims.
- [x] Raw `soil_adc_raw` MQTT/discovery semantics, OLED rows, 30-second cadence/power-off,
  diagnostic mode and AtmosMesh v1 remain unchanged.
- [x] Full native/build/compatibility/polarity/diagnostic/check/secret gates pass before commit; no
  flash, self-review or merge occurs.

## Validation plan

Add failing native tests for canonical polarity, calibration validation/classification, final LED
priority and diagnostics before production behavior. Compose the pure policy into the thin Grove
runtime, then compile canonical and common-cathode normal/visual images plus all existing product
and compatibility gates. Do not set real calibration thresholds or flash in this lane.

## Evidence

- Operator confirmed on 2026-08-24 that only the inverted diagnostic produced correct physical
  colors: installed wiring is D6 red, D0 green, common-anode. Normal firmware was restored with an
  ad hoc common-anode flag; this story removes that future footgun.
- **Red, 2026-08-24:** after tests were added first, `task test` failed at native compilation because
  the requested `atmosmesh/soil_status.hpp` policy boundary did not exist.
- **Green, 2026-08-24:** 105/105 native tests pass. New cases cover canonical common-anode profile,
  both valid raw directions, disabled/unknown/range/equal/order failures, raw zero, missing and
  acquisition-failed states, the complete system/MQTT/soil priority, and non-secret serial truth.
- **Build matrix, 2026-08-24:** `task build-all`, compatibility `task build`/`task build-grove`,
  direct `esp32dev`/`esp8266-grove`, canonical/common-cathode normal images, canonical and
  common-cathode visual diagnostics, and illustrative valid higher-is-wetter/lower-is-wetter
  calibration configurations all pass. Canonical v1 used 48,216 bytes RAM / 998,441 bytes flash;
  the final generated-secret Grove image used 45,140 bytes RAM / 476,831 bytes flash. `task check`,
  `git diff --check` and the tracked/generated-secret audit pass.
- No firmware was flashed during implementation. Calibration remains disabled in the canonical
  image until controlled dry/wet observations establish direction and both thresholds; raw
  MQTT/HA semantics are unchanged.
- **Review regression, 2026-08-24:** a failing native compile first proved the policy lacked an
  explicit core-acquisition-attempt state. The green policy/runtime now treats absent DHT/BMP
  readings as boot-time unknown/amber until `sample_sensors()` actually runs; missing readings
  after that first attempt are a real core error/red. MQTT-configured-offline and every later
  priority remain unchanged.
- **Reviewed hardware evidence, 2026-08-24:** after independent approval of head `8fca62d`, the
  coordinator ran `ESP_PORT=/dev/cu.usbserial-0001 task flash-v1-5`. Esptool identified the
  ESP8266EX/26 MHz target, wrote 480,976 bytes, verified the hash and hard-reset. More than 30
  seconds of serial reported DHT11 26.0 °C / 35–37% RH, BMP180 26.1–26.3 °C /
  981.5–981.6 hPa, uncalibrated light 393–401 µs and raw soil ADC 213 from five samples with
  software `power=off`. After the soil sample, serial reported
  `status-led: amber reason=soil-calibration-needed red=LOW green=LOW` and
  `soil-led-status: amber reason=soil-calibration-needed raw=213 calibration=disabled
  direction=unknown dry=unset acceptable=unset`. This proves the canonical common-anode logical
  amber drive and calibration-safe policy at runtime. It does not prove visible LED colour,
  physical switched-rail power-off or probe calibration. Operator visual confirmation and
  controlled dry/wet reference measurements remain pending.
