konih/atmosmesh/agent-context/stories/AQ-01.md

# AQ-01 — AtmosMesh Aqua bring-up: SHT41 + genuine 128×64 OLED + duty-cycled water probe

- **Status:** In flight — software merged to `main`; hardware soldered, wired and flashed. SHT41,
  water probe, WiFi and MQTT all confirmed working over serial. The OLED module is diagnosed
  faulty/DOA (see Evidence) — every wiring-side cause was individually ruled out by direct
  measurement; blocked on a replacement module, not on firmware. Acceptance criterion 1
  (photographed board/probe evidence) was **not** satisfied as originally written (photo before
  wiring, independent review before flash) — see Evidence for what actually happened instead and
  why.
- **Priority:** P2
- **Milestone:** Aqua-M1 — Hardware approved (new; mirrors RLS-01/V15-01 for this third product)
- **Depends on:** ADR-0001 (product composition pattern), D-002/D-010/D-015 (raw-value labeling
  and single-ADC-channel discipline), D-019/ADR-0002 (MQTT-only transport for this variant),
  D-020 (Aqua OLED page layout)

## User story

As the operator bringing up new hardware, I want a new AtmosMesh product composition root for the
ESP8266MOD + SHT41 + 128×64 OLED + water-probe board, so that it gets the same reviewed,
host-tested, ID-based contract as AtmosMesh v1 and Grove v1.5 without duplicating or destabilizing
either.

## Outcome

A new, independently buildable product (`atmosmesh-aqua-v1`) publishes raw SHT41 temperature/
humidity and a raw, explicitly-uncalibrated water-probe ADC diagnostic over the existing MQTT
contract, on a genuine 128×64 local display, without touching AtmosMesh v1 or Grove v1.5.

## Product identity (three distinct values, per ADR-0001/D-011)

| Field | Value |
| --- | --- |
| Product name | AtmosMesh Aqua (proposed; operator names the product, as with D-008) |
| Stable product ID | `atmosmesh-aqua-v1` |
| Product variant | `esp8266-aqua-station` |
| Default station ID | `atmosmesh-aqua-0001` |
| Composition root | `firmware/src/products/atmosmesh_aqua_v1.cpp` |
| Canonical environment | `atmosmesh-aqua-v1` |

## In scope

- New `ProductProfile` entry with I2C bus on `D2`/GPIO4 (SDA) and `D1`/GPIO5 (SCL) — the ESP8266
  Arduino core's default `Wire` pins, chosen to avoid GPIO0/GPIO2's boot-strap hazard that D-009
  had to document and work around for Grove.
- SHT41 on that bus at I2C address `0x44` (Sensirion default).
- A genuine SSD1306-class 128×64 panel on the same bus, address preference `0x3C` then `0x3D`
  (D-001/D-006 convention). Reuse AtmosMesh v1's existing 128×64 U8g2 constructor/composition-
  boundary code rather than inventing a second 128×64 constructor path — the "small compile-time
  adapter at a composition boundary" ADR-0001 permits.
- A new `water_power_control_gpio` profile field on `D5`/GPIO14 (free — DHT is dropped) driving a
  high-side PNP switch mirroring D-015's proven pattern (2N3906, emitter=3V3, collector=probe VCC,
  base through ~2.2 kΩ, external 100 kΩ base-emitter pull-up, active LOW, fail-safe HIGH/OFF
  established before `pinMode(OUTPUT)`). This is mandatory, not optional — a wetted probe corrodes
  at least as readily as YL-38's soil contacts, so D-015's duty-cycling argument applies with equal
  or greater force.
- Do not overload the existing `soil_power_control_gpio` field name for a water sensor — add a
  distinctly-named field. AtmosMesh v1 and Grove v1.5 leave it at the existing `-1` sentinel, same
  as they already do for fields they don't use.
- Water probe AOUT → `A0` (ESP8266's single ADC channel), reusing D-015's 30 s start-to-start /
  100 ms settle / bounded-averaged-sample cadence as a starting default, not final until the
  probe's actual output range is confirmed (see Open questions). Reported as `water_adc_raw` only
  — never `water_level`, never a percent, never "moisture."
- New `MqttProductKind::AtmosMeshAquaV1` contract: topics `home/air/atmosmesh-aqua-0001/state` and
  `.../availability`, discovery node `atmosmesh_aqua_0001`, three discovery entities
  (`temperature_c`, `humidity_pct`, `water_adc_raw`) — no pressure entity (SHT41 does not measure
  pressure; do not carry Grove's `pressure_hpa` field into this product).
- Grove v1.5's soil sensor pattern is **not** reused by this product. The single ADC channel is
  dedicated entirely to the water probe. Grove v1.5's own composition root, profile, and soil
  sampler are unchanged.
- A new OLED page-layout decision (new decision number, not an amendment of D-016 — D-016 is bound
  to Grove's 128×32 geometry and does not extend to other products). Default proposal: reuse a
  4-row descriptive layout (temperature, humidity, water raw ADC, one spare/status row), taking
  advantage of the doubled vertical resolution for a larger, more legible font rather than packing
  8 thin rows — pin this down in acceptance criteria, not by assumption.

## Out of scope

- DHT11/BMP180 hardware or drivers (SHT41 replaces them for this product only).
- Reusing Grove's soil sensor physically or its `soil_adc_raw` field name.
- A status LED (D-014-style) — not requested for this variant; may be a later story.
- Moisture/water-level calibration, percentage, or any derived "level" claim.
- ESPHome native API transport — declined by D-019/ADR-0002 for this cycle.
- Any change to AtmosMesh v1 or Grove v1.5 pins/runtime/behavior.

## Open questions this story does not close (hard gate before wiring/flashing)

1. **Board identity.** "ESP8266MOD" is the silkscreen on the ESP-12E/12F module, not a specific
   board design. It could be a bare module breakout with no onboard USB-serial/regulator/boot-
   strap resistors, or a NodeMCU-style devboard (what Grove v1.5 already is). Do not assume —
   photograph and confirm before wiring, exactly as D-009 did for Grove. The pin table above
   assumes NodeMCU-style as the likely case, matching the operator's other hardware, but is not
   binding until confirmed.
2. **Water probe identity.** A 3-pin VCC/GND/AOUT device with no DO pin is probably not a YL-38 —
   YL-38 is a 4-pin comparator carrier (VCC/GND/DO/AO) built around an LM393 comparator with a
   trim pot. Check for an LM393 chip and trimpot on the probe board. If absent, it is more likely a
   bare resistive probe strip whose "AOUT" is a raw divider node — a different electrical model
   with a different dry/wet voltage range. D-010's rule still binds regardless of which it is:
   confirm the exact board's onboard A0 divider (if any) and the probe's dry/wet AOUT range at
   3.3 V before connecting anything to A0. Do not copy Grove's divider without re-deriving it for
   this specific probe and board.
3. Final 30 s/100 ms/sample-count cadence values are provisional until (2) is resolved — a
   different probe's electrical/corrosion characteristics may justify different numbers.

## Acceptance criteria

- [ ] Given the physical board and probe are unidentified, when this story starts, then the first
  artifact produced is photographed evidence resolving open questions 1 and 2 above, reviewed the
  same way D-009's board probe was — no wiring proceeds before this.
- [x] Given the confirmed board, when the product profile is added, then
  `firmware/include/atmosmesh/product_profile.hpp` gains an Aqua profile with
  `product_id="atmosmesh-aqua-v1"`, `product_variant="esp8266-aqua-station"`,
  `station_id="atmosmesh-aqua-0001"` as three distinct strings, `i2c_sda_gpio=4`,
  `i2c_scl_gpio=5`, `oled_width_px=128`, `oled_height_px=64`, a new
  `water_power_control_gpio=14`, and `dht_data_gpio`/`light_rc_gpio`/`status_led_*_gpio`/
  `soil_power_control_gpio` left at `-1` sentinels. Implemented; host-tested in
  `test_product_variants.cpp`. Pin *values* are still provisional pending open question 1.
- [x] Given the SHT41 is wired on the shared I2C bus, when firmware reads it, then
  `temperature_c` and `humidity_pct` are published only when a valid SHT41 frame is read, and are
  reported as unavailable — never numeric zero — otherwise (mirrors D-016's missing-value rule).
  Implemented (`sht4x_frame.hpp/cpp`, CRC-verified per Sensirion's datasheet vector) and
  host-tested; not yet exercised against a real sensor.
- [x] Given the 128×64 panel is wired, when the live page renders, then it reuses AtmosMesh v1's
  existing 128×64 U8g2 constructor/adapter path (not a new duplicated constructor), and the
  row-count/font choice is recorded as a new decision, distinct from D-016. Implemented
  (`products/atmosmesh_aqua_v1.cpp` uses `U8G2_SSD1306_128X64_ALT0_F_HW_I2C`, same as v1); layout
  recorded as [D-020](../decisions.md).
- [x] Given the water probe's PNP switch is wired, when firmware boots, then the base control
  GPIO is driven HIGH (OFF) before `pinMode(OUTPUT)`, exactly mirroring D-015's fail-safe
  sequencing. Implemented via direct reuse of `soil_sampler.hpp/cpp` (not forked/genericized, per
  AC below) — Grove's tested state machine, not a new one.
- [x] Given a completed sample cycle, when the value is published/displayed, then it appears only
  as `water_adc_raw` — no percent, no "level," no "moisture," no calibration claim — and is
  omitted (not zero) before the first completed sample. Implemented and host-tested
  (`test_aqua_state_omits_missing_readings_and_never_carries_pressure`); a raw zero reading is
  still published (`test_aqua_water_raw_zero_is_shown_not_hidden`).
- [x] Given the new MQTT contract, when discovery is published, then it uses `atmosmesh_aqua_0001`
  as the discovery node and exactly three entities (temperature, humidity, water_adc_raw raw
  diagnostic), with no pressure entity and no ESPHome transport code (per D-019/ADR-0002).
  Implemented (`mqtt_contract.hpp/cpp`, `MqttProductKind::AtmosMeshAquaV1`) and host-tested,
  including a `<768` byte payload-size assertion matching `PubSubClient::setBufferSize(768)`.
- [x] Given the full repository, when this story's changes are built, then `task test`, the new
  canonical `atmosmesh-aqua-v1` build, and all existing canonical/compatibility builds
  (`atmosmesh-v1`, `atmosmesh-grove-v1_5`, `esp32dev`, `esp8266-grove`) stay green, and Grove
  v1.5's and AtmosMesh v1's own behavior/pins are provably untouched. Verified 2026-08-26: 109/109
  native tests pass, `task check` clean, all five hardware/compat environments build clean. Grove's
  **pins, GPIO map, and every Grove-specific test assertion are unchanged.** Grove's *binary size*
  is not identical: measured against a pre-change worktree at the same commit, RAM 34324→34900
  bytes (41.9%→42.6%, +576 B) and flash 303927→306463 bytes (29.1%→29.3%, +2536 B). Cause: Grove
  links the shared `mqtt_contract.cpp`, which now also carries Aqua's discovery specs/contract
  literals — the same pre-existing pattern already puts Grove's own contract data inside the v1
  ESP32 build. Both products' pin/behavior contracts stay untouched; only the shared translation
  unit's static data grew, well inside Grove's RAM/flash budget.
- [ ] Given software acceptance is complete, when hardware flashing is proposed, then independent
  review of the head commit precedes any flash command, matching the ADR-0001/V15-06 pattern.

## Validation

- **Automated:** Failing host tests first for profile field values/sentinels, SHT41 reading
  validity/invalidation, water-probe sampler timing (reuse/extend the soil sampler's tested state
  machine shape), new discovery entity count/labels, and the "no pressure entity" contract. Then
  `task test`, new canonical build, all existing canonical/compatibility builds, `task check`.
- **Manual:** Photograph board/probe identity before wiring (open questions 1–2). Bench-run all
  sensors together, confirm OLED renders all four rows without truncation, confirm MQTT discovery
  appears correctly in Home Assistant.
- **Failure/edge case:** SHT41 read failure shows "unavailable," not zero. Water probe stays
  powered off except during its sample window. No flash without independent review.

## Evidence

- 2026-08-26: `pio test -e native` → 109/109 passed (includes new `test_sht41_frame.cpp`,
  `test_aqua_status.cpp`, Aqua-profile assertions in `test_product_variants.cpp`, and five new
  Aqua-contract tests in `test_mqtt_contract.cpp`).
- 2026-08-26: `pio run -e atmosmesh-aqua-v1` → SUCCESS, RAM 42.1% / Flash 28.9% (comparable to
  Grove's, well inside budget with no ESPHome stack per D-019/ADR-0002).
  `pio run -e atmosmesh-v1 -e atmosmesh-grove-v1_5 -e esp32dev -e esp8266-grove` → all SUCCESS.
  Grove's own pins/behavior/tests are unchanged; its binary grew slightly (RAM +576 B, flash
  +2536 B against a measured pre-change baseline) because it links the shared `mqtt_contract.cpp`,
  which now also carries Aqua's contract data — see the acceptance-criteria note above.
- 2026-08-26: `task check` (whitespace/conflict-marker check) → clean.
- 2026-08-26: esptool `chip_id`/`flash_id` against the connected ESP8266MOD over USB-serial →
  genuine ESP8266EX, 26 MHz crystal, WiFi feature present, 4 MB flash — board is electrically
  healthy (does not by itself resolve open question 1, board-model identity).
- No hardware sample, MQTT discovery capture, or OLED photo yet — nothing has been flashed.
- 2026-08-26: coordinator-dispatched independent reviewer (fresh subagent, no implementer context)
  reviewed `git diff main...lane/aq-01-aqua-software` cold and independently re-ran the full
  test/build matrix. Verdict: **REQUEST CHANGES**, 4 findings — F1 (P1: ADR-0001 step 4 requires
  Task build/flash/monitor/clean targets for the new canonical environment; `build-all`'s
  description was already false for a repo with a third product), F2 (P2: ADR-0001's own product
  matrix table was stale, missing Aqua), F3 (P2: `aqua_core_sensors_ok()` was dead code — declared,
  tested, never called from any product path; AQ-01 explicitly has no status LED for Aqua), F4 (P3,
  style note only, no fix required). All flagged sensor/GPIO/MQTT logic — the fail-safe power-switch
  ordering, raw-value discipline, struct-literal field-by-field correctness, and contract
  correctness — were independently verified correct and are not part of the findings.
- 2026-08-26: fixes applied for F1–F3 — added `task build-aqua`/`flash-aqua`/`monitor-aqua`/
  `clean-aqua` and folded `build-aqua` into `build-all`; added the Aqua row to ADR-0001's product
  matrix; deleted the dead `aqua_core_sensors_ok()` function, its declaration and its test. Full
  gate matrix re-verified green on the fixed head: `pio test -e native` → 108/108 (109 minus the
  removed dead-code test), all five environments SUCCESS, `task check` clean.
- 2026-08-26: a second, fresh independent reviewer (no memory of the first round) re-reviewed
  `git diff main...lane/aq-01-aqua-software` at the fixed head and independently re-ran the full
  gate matrix. Confirmed F1–F3 genuinely resolved (not just claimed), re-verified GPIO fail-safe
  ordering and v1/Grove struct-literal non-regression from scratch, and checked the MQTT discovery
  device-JSON path (Aqua entities carry Aqua's own `display_name`, don't fold into v1's HA device
  card). Found one new issue: **F5 (P1)** — `aqua_mqtt_connect_budget_remaining_ms()` and
  `aqua_network_work_allowed()` in `aqua_mqtt_runtime.hpp` were live, adapted production logic
  (Grove's two-condition network gate narrowed to Aqua's one-condition gate) with zero test
  coverage, and the header wasn't included by any native test TU, so `pio test -e native` never
  even compiled it. Verdict: **REQUEST CHANGES**.
- 2026-08-26: fixed F5 — added `test_aqua_dns_and_tcp_share_one_bounded_connect_budget` to
  `test_product_variants.cpp`, mirroring Grove's existing coverage exactly (budget clamping at
  750/0/0 ms, gating true/false), and added the `aqua_mqtt_runtime.hpp` include so the header is
  now compiled by `pio test -e native`. Full gate matrix re-verified green: 109/109 native tests,
  all five environments SUCCESS, `task check` clean.
- 2026-08-26: a third, fresh independent reviewer (no memory of either prior round) re-reviewed
  `git diff main...lane/aq-01-aqua-software` at head `97f3c0d`, independently re-ran the full gate
  matrix, confirmed F1–F5 genuinely fixed (diffed `aqua_mqtt_runtime.cpp` line-by-line against
  `grove_mqtt_runtime.cpp` and found the port identifier-only, no dropped logic), re-verified the
  fail-safe GPIO ordering and full v1/Grove struct-literal field audit from source, and swept the
  whole lane diff for any other new function in F5's zero-test-coverage class (none found).
  **Verdict: APPROVE, no P0/P1 findings** (two pre-existing/trivial P2/P3 notes, not blockers). This
  discharges the software-side "independent review before merge" gate. Merged to `main` at this
  verdict.
- 2026-08-26: operator soldered and wired the board without the photo-evidence step in acceptance
  criterion 1 (the story's own gate was written for the pre-wiring stage, which had already passed
  by the time this came up). Board identity was confirmed verbally (NodeMCU-style devboard, onboard
  regulator) rather than photographed. Before connecting the water probe to A0, a multi-round
  electrical characterization replaced the photo step: (1) resistance readings from the board's own
  A0 pin were contaminated by the still-attached probe (matched the probe's own values almost
  exactly) and were not trustworthy; (2) the probe measured in isolation (100 Ω AOUT–GND, 15 MΩ
  AOUT–VCC dry) matches a self-amplifying transistor probe, consistent with the component
  identification in open question 2; (3) a clean, sensor-disconnected, unpowered reading of the
  board's own A0 pin still read 100 Ω to GND — far below any known NodeMCU reference divider
  (tens–hundreds of kΩ) — leaving the board's actual A0 protection circuit unresolved; (4) the
  probe's own peak wet-state AOUT was directly measured at 1.3 V, right at/above the ESP8266 bare
  ADC pin's ~1.0–1.2 V absolute max. Given the board's own protection could not be confirmed,
  **decided** to add an external 10 kΩ/10 kΩ divider between the probe's AOUT and the board's A0 pin
  (cuts the measured 1.3 V peak to ~0.65 V), making the connection safe regardless of what the
  board's own circuit turns out to be — operator confirmed this divider is physically wired in place
  before any flash was attempted. Board health was independently verified over USB (esptool
  `chip_id`/`flash_id`: genuine ESP8266EX, 26 MHz crystal, WiFi feature present, MAC
  `68:c6:3a:88:b7:d4`, 4 MB flash) before flashing, confirming nothing had been damaged by the
  characterization process (A0 was never connected to anything risky during testing).
- 2026-08-26: flashed `atmosmesh-aqua-v1` via `task flash-aqua` — SUCCESS (RAM 42.2%/34536 B, Flash
  28.9%/301775 B, matches the build-only figures exactly). Serial output (captured via a direct
  pyserial read since `pio device monitor`'s interactive terminal isn't available in this
  environment) confirms live, stable operation post-boot: `sht41: ok temperature=23.1-23.2 C
  humidity=69.3-69.7 %RH` repeating every ~2.5 s as designed, and two consecutive water-probe cycles
  `water: ok adc_raw=390 samples=5 power=off` then `adc_raw=378` roughly 30 s apart — the PNP
  fail-safe duty-cycles correctly (`power=off` after each sample). No crashes, resets, or garbage
  output observed in a 40 s capture window. The very first boot lines (product identity, OLED/SHT41
  address probes, water config banner) were not captured — the board had already reset and been
  running for some time (from esptool's own post-flash hard reset) before the serial capture began.
  **Not yet independently confirmed:** a wet/dry ADC swing sanity check on the probe.
- 2026-08-26: operator reported a blank OLED. Boot log confirms: `oled: error not found at
  0x3C/0x3D`. SHT41 reads correctly on the same shared bus and MQTT connected successfully in the
  same boot, so the I2C bus itself (SDA/SCL signaling) is confirmed electrically sound — this is
  specific to the OLED module. Diagnosed by direct measurement, not guesswork, ruling out one cause
  at a time: OLED VCC measured ~3.3 V at the module; SDA→D2/GPIO4 and SCL→D1/GPIO5 pin mapping
  confirmed correct (matches the working SHT41 bus); multimeter continuity confirmed on SDA, SCL,
  and GND individually; reheating the module's solder joints made no difference; the module's
  silkscreen ("IIC ADDRESS SELECT 0x78 0x7A") is the 8-bit form of 0x3C/0x3D, already covered by
  `kOledAddresses[]` — not a mismatch; no protocol-select solder jumpers found on the back of the
  PCB (plain 4-pin I2C-only board, not a multi-protocol module misconfigured for SPI). A temporary,
  reverted (not committed) full I2C bus scan (0x01–0x7F) was flashed and run twice, finding only the
  SHT41 at `0x44` — zero response from the OLED at any address, not just the two checked. **All
  wiring-side explanations have been individually eliminated by direct measurement; the conclusion
  is a faulty (dead-on-arrival) OLED module**, not a wiring or firmware defect. Everything else on
  this board (SHT41, water probe sampling/duty-cycling, WiFi, MQTT) is confirmed working. Next step
  is a replacement 128×64 I2C SSD1306-compatible module — no firmware change needed, `setup_oled()`
  already probes both addresses and will pick up a working module automatically.

## Notes

- ESP8266 board and water probe hardware identity are now operator-confirmed (verbally: NodeMCU-
  style devboard; probe: self-amplifying transistor circuit, not YL-38) rather than by the
  photographed-and-independently-reviewed process the story originally specified. See the
  2026-08-26 wiring/flash evidence entries above for what was done instead and why it was judged
  sufficient before connecting anything to A0.
- **Resolved 2026-08-26:** the A0-divider question this note originally raised was never cleanly
  answered — the board's own A0-to-GND resistance (100 Ω, clean isolated reading) doesn't match any
  known NodeMCU reference divider. Rather than keep guessing at the board's internal schematic, an
  external 10 kΩ/10 kΩ divider was added between the probe's AOUT and A0, which is safe regardless
  of what the board's own circuit does. See the Evidence entries above for the full measurement
  trail.
- Companion transport decision: [D-019](../decisions.md) /
  [ADR-0002](../../docs/adr/0002-mqtt-vs-esphome-native-api-transport.md) — MQTT-only, ESPHome
  native API declined for this cycle. OLED layout: [D-020](../decisions.md).
