konih/atmosmesh/agent-context/stories/V15-02.md

# V15-02 — Shared multi-variant firmware architecture

- **Status:** Done
- **Priority:** P0
- **Depends on:** V15-01
- **Objective:** Build ESP32 v1 and ESP8266 Grove v1.5 from one PlatformIO project without cloning
  the complete ESP32 application.

## Scope

- Add a 4 MB NodeMCU-style ESP8266 PlatformIO environment.
- Add a thin Grove entrypoint/profile and shared pure formatting/domain behavior while preserving
  the existing ESP32 entrypoint.
- Name both product composition roots and add compile-time identity metadata for both.
- Add canonical product environments/tasks and retain existing compatibility commands.
- Propose and document the multi-product composition ADR.

## Out of scope

- Physical upload, MQTT/Wi-Fi, sensor calibration, or refactoring unrelated ESP32 subsystems.

## Acceptance criteria

- [x] Native tests prove Grove identity, pins, health formatting and missing-value behavior.
- [x] Native tests prove stable identity/profile metadata for both first-class products.
- [x] Both composition roots are explicitly named under `src/products/`; native excludes them.
- [x] ADR-0001 records context, decision, alternatives, consequences, migration and validation.
- [x] Canonical builds, `build-all`, compatibility builds and repository gates pass.
- [x] No secrets or generated binaries are tracked.

## Validation plan

Add failing native tests before new profile/utility behavior. Pure source moves and documentation
use build/gate evidence rather than contrived tests. Build each canonical and compatibility target.

## Evidence

- **Red, 2026-08-24:** `task test` failed to compile
  `test_grove_variant.cpp`: `atmosmesh/grove_status.hpp` did not exist.
- **Green, 2026-08-24:** initial `task test` passed 73 tests across native MQTT and device suites,
  including valid-zero, missing and partial-failure Grove states.
- **Review red/green, 2026-08-24:** a new test initially failed because the BMP presence/action API
  did not exist; it now proves loss invalidates plausible prior values and return requires
  initialization before read. The native total is 74 passing tests.
- `task build` passed for the unchanged `esp32dev` target (ESP32 image 72.7% flash, 14.6% RAM).
- `task build-grove` passed for `nodemcuv2` / ESP8266, 4 MB flash (image 27.1% flash, 37.1% RAM).
- PlatformIO filters originally preserved the ESP32 entrypoint and selected Grove plus shared
  `grove_status.cpp`; the later structural migration names both roots under `src/products/`. No
  ESP32 behavior/profile-consumption refactor is claimed. No upload target was invoked.
- `task check` and a separate `git diff --check` passed; `git status --short` contained no tracked
  secrets or generated `.pio` output.
- **Multi-product red, 2026-08-24:** `task test` failed because
  `atmosmesh_v1_profile()` did not exist. The compile-time v1 product contract now has a test beside
  the Grove contract. A follow-up red test required separate SDA/SCL boot-strap metadata so the v1
  GPIO5 SDA caveat and Grove GPIO0 SCL caveat cannot be conflated; both are now explicit.
- **Multi-product green, 2026-08-24:** `task test` passed 75 tests. Native compilation excludes
  `src/products/*` and includes shared host-testable modules once.
- **Identity-contract red/green, 2026-08-24:** review found Grove variant metadata was being used
  where ADR-0001 defines a distinct stable product ID. Tests first failed on the missing
  `ProductProfile::product_id`; both profiles now declare product ID and variant separately.
- **Identity-separation red/green, 2026-08-24:** strengthened profile tests first failed because v1
  used `atmosmesh-v1` for both product ID and variant. V1 now retains its D-007 product ID and uses
  the distinct `esp32-full-station` variant; tests assert product ID, variant and station ID are
  pairwise distinct for both products.
- `task build-v1` selected only `src/products/atmosmesh_v1.cpp` and reproduced the existing v1
  image size (72.7% flash, 14.6% RAM).
- `task build-v1-5` selected only `src/products/atmosmesh_grove_v1_5.cpp` plus Grove shared status
  logic (27.2% flash, 37.3% RAM on the 4 MB ESP8266 target).
- `task build-all`, compatibility `task build` / `task build-grove`, and direct compatibility
  environments `esp32dev` / `esp8266-grove` all passed.
- `task check` and separate `git diff --check` passed. No upload command was run.
