konih/atmosmesh/agent-context/stories/V15-07.md

# V15-07 — Grove descriptive four-row OLED page

- **Status:** Blocked on operator visual hardware confirmation
- **Priority:** P1
- **Depends on:** V15-03 through V15-06 software contracts
- **Objective:** Use every row of the 128×32 OLED for a plainly labelled fitted measurement so a
  reader does not need to decode product or health-bit abbreviations.

## Scope

- Replace the normal product/name row and combined `D1B1` health row with exactly four labelled
  measurement rows: DHT11 temperature/humidity, BMP180 pressure, raw RC light time and raw soil ADC.
- Keep each row clipping-safe in the compiled 5×7 font on 128 pixels.
- Name missing values by metric and never turn unavailable into numeric zero.
- Preserve detailed serial sensor diagnostics and the separate bi-color health LED contract.
- Prove Grove MQTT state and retained Home Assistant discovery still expose exactly the five fitted
  public measurements: `temperature_c`, `humidity_pct`, `pressure_hpa`, `light_charge_us` and
  `soil_adc_raw`.

## Out of scope

- AtmosMesh v1 display/runtime changes, a product/name row, OLED menus, BMP temperature as a public
  measurement, lux/moisture calibration, MQTT topic changes, or hardware flashing.

## Acceptance criteria

- [x] Valid readings render four descriptive rows equivalent to `T:25.0C RH:36%`, `P:982.7hPa`,
  `Light:401us`, `Soil:214`, within the OLED width.
- [x] Missing/fault values explicitly retain their metric labels (`T:--`, `RH:--`, `P:ERR`,
  `Light:--`, `Soil:--`); valid numeric zero remains visible.
- [x] The normal page contains neither product/name text nor `D1B1`/other anonymous health bits.
- [x] Serial diagnostics and AtmosMesh v1 behavior remain unchanged.
- [x] Native tests prove all five Grove MQTT state keys and five truthful HA discovery objects remain
  present, with DHT11 as `temperature_c` and raw-only light/soil semantics.
- [x] Native tests, both canonical builds, compatibility builds, repository checks and secret audit
  pass before commit. No flash, self-review or merge occurs in this lane.

## Validation plan

Add failing native expectations for valid, missing, partial and numeric-zero OLED rows before
changing the formatter. Strengthen the existing Grove MQTT/discovery tests to assert the exact five
keys/object IDs. Run the full product gate matrix and record red/green evidence here.

## Evidence

- Operator observed `L401us S214 D1B1` and requested descriptive values in place of the product row
  and cryptic DHT/BMP bits. Contract accepted 2026-08-24.
- **Red, 2026-08-24:** six native assertions failed against the old product row, combined light/soil
  row and anonymous DHT/BMP bits. Exact-five MQTT state/discovery coverage already passed.
- **Green, 2026-08-24:** 92 native tests pass with four labelled, width-bounded rows; independent
  missing DHT metrics, pressure fault, missing light/soil and four valid numeric-zero values are
  explicit. The five MQTT keys/discovery object IDs remain exactly temperature, humidity, pressure,
  raw light microseconds and raw soil ADC.
- **Full gates, 2026-08-24:** `task test` passed 92/92; `task build-all`, `task build`,
  `task build-grove`, direct `esp32dev` / `esp8266-grove` compatibility builds and the common-anode
  Grove build passed. AtmosMesh v1 remains 14.6% RAM / 72.8% flash; Grove is 42.1% RAM / 29.3%
  flash. `task check`, `git diff --check` and the generated-secrets ignore/untracked audit passed.
  No flash command was run.
- **Reviewed flash/runtime, 2026-08-24:** independent review approved cumulative head `4e4a820`.
  The coordinator then ran `ESP_PORT=/dev/cu.usbserial-0001 task flash-v1-5`; esptool identified the
  ESP8266EX/26 MHz target, wrote 310,224 bytes, verified the hash and hard-reset. More than 30
  seconds of 115200-baud serial reported `mqtt: connected`, a green/healthy logical LED command,
  DHT11 25.0 °C / 36% RH, BMP180 25.3–25.7 °C / 982.1–982.4 hPa, uncalibrated light 420–492 µs,
  and `soil: ok adc_raw=214 samples=5 power=off`; DHT/BMP/light health was okay. This proves the
  flashed runtime and serial commands, not broker-side MQTT receipt/discovery, visible LED colour,
  or visible OLED pixels/layout.
- Software review and flash acceptance are complete. Operator visual confirmation of the four
  rendered rows remains pending.
