konih/atmosmesh/docs/assets/inventory/esp32-2432s028-cyd-annotated-2026-09-19.png

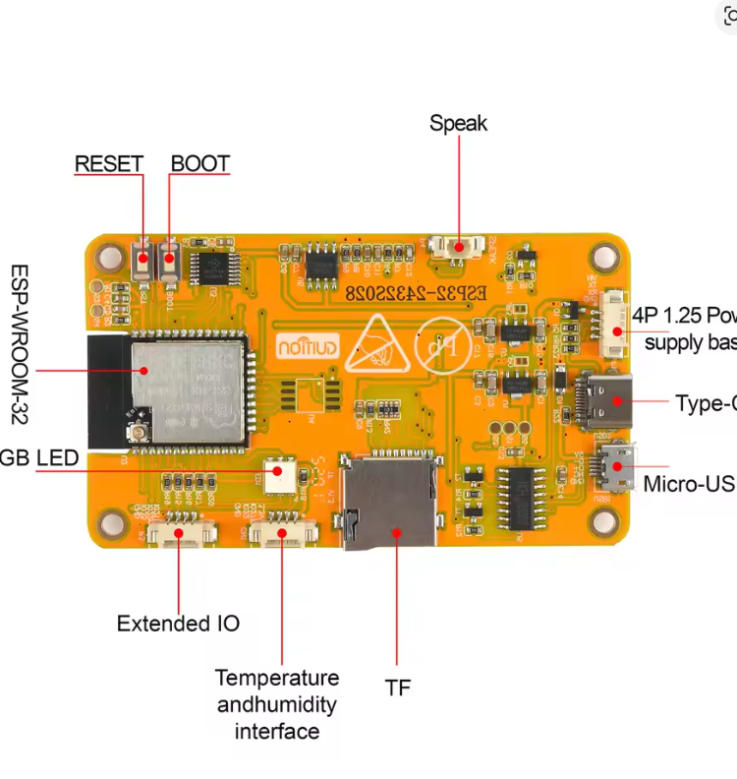
docs/assets/inventory/esp32-2432s028-cyd-annotated-2026-09-19.png
