konih/atmosmesh/docs/assets/inventory/gc9b72-round-tft-front-2026-09-19.png

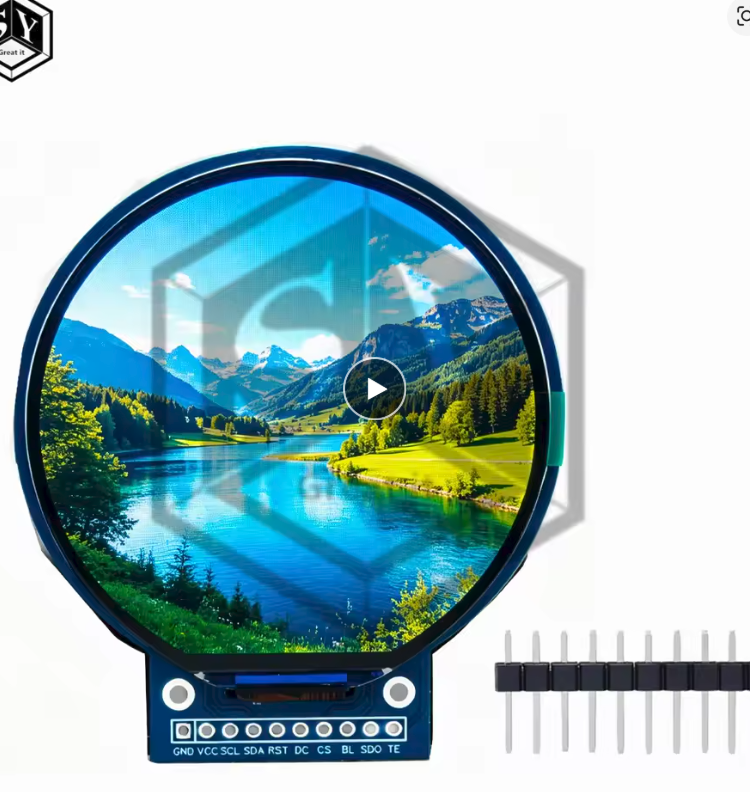
docs/assets/inventory/gc9b72-round-tft-front-2026-09-19.png
