konih/atmosmesh/docs/assets/inventory/lipo-603048-1000mah-label-2026-09-19.png

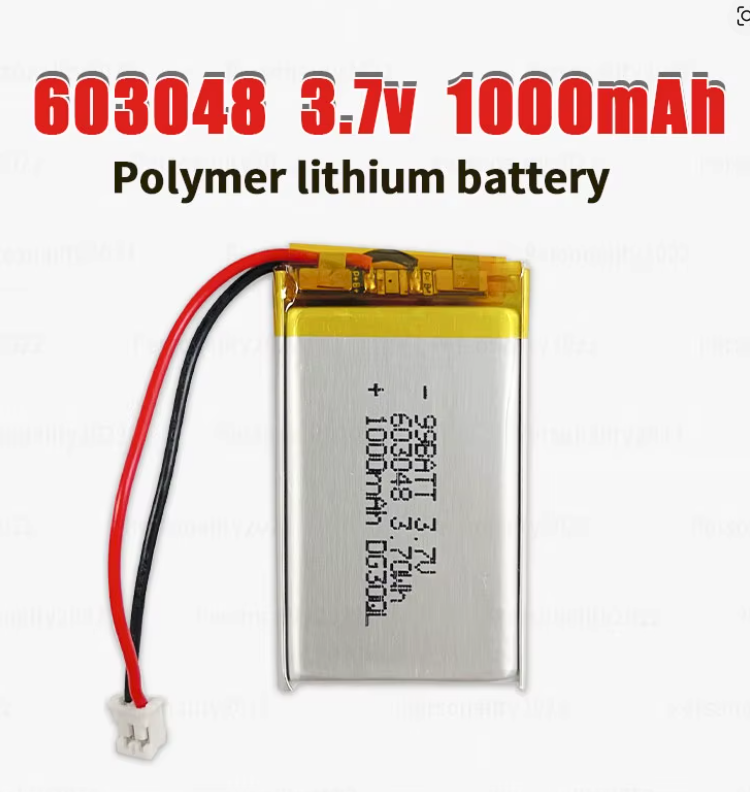
docs/assets/inventory/lipo-603048-1000mah-label-2026-09-19.png
