konih/atmosmesh/docs/assets/inventory/tp4056-zj-chc-v2-charger-listing-2026-09-19.png

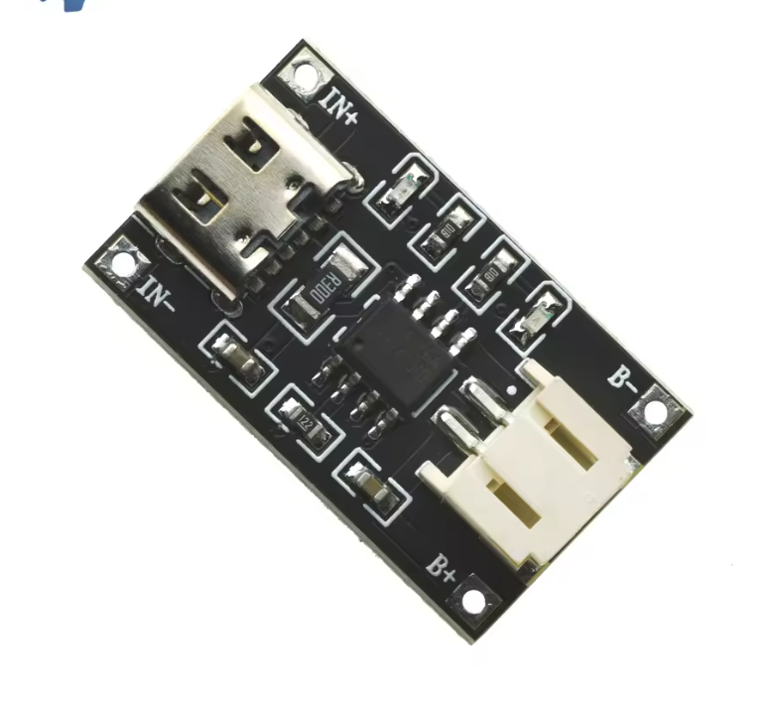
docs/assets/inventory/tp4056-zj-chc-v2-charger-listing-2026-09-19.png
