konih/atmosmesh/hardware/kicad/atmosmesh-room/atmosmesh-room.kicad_pcb

## KiCad design hardware/kicad/atmosmesh-room/atmosmesh-room.kicad_pcb (2026-08-28)

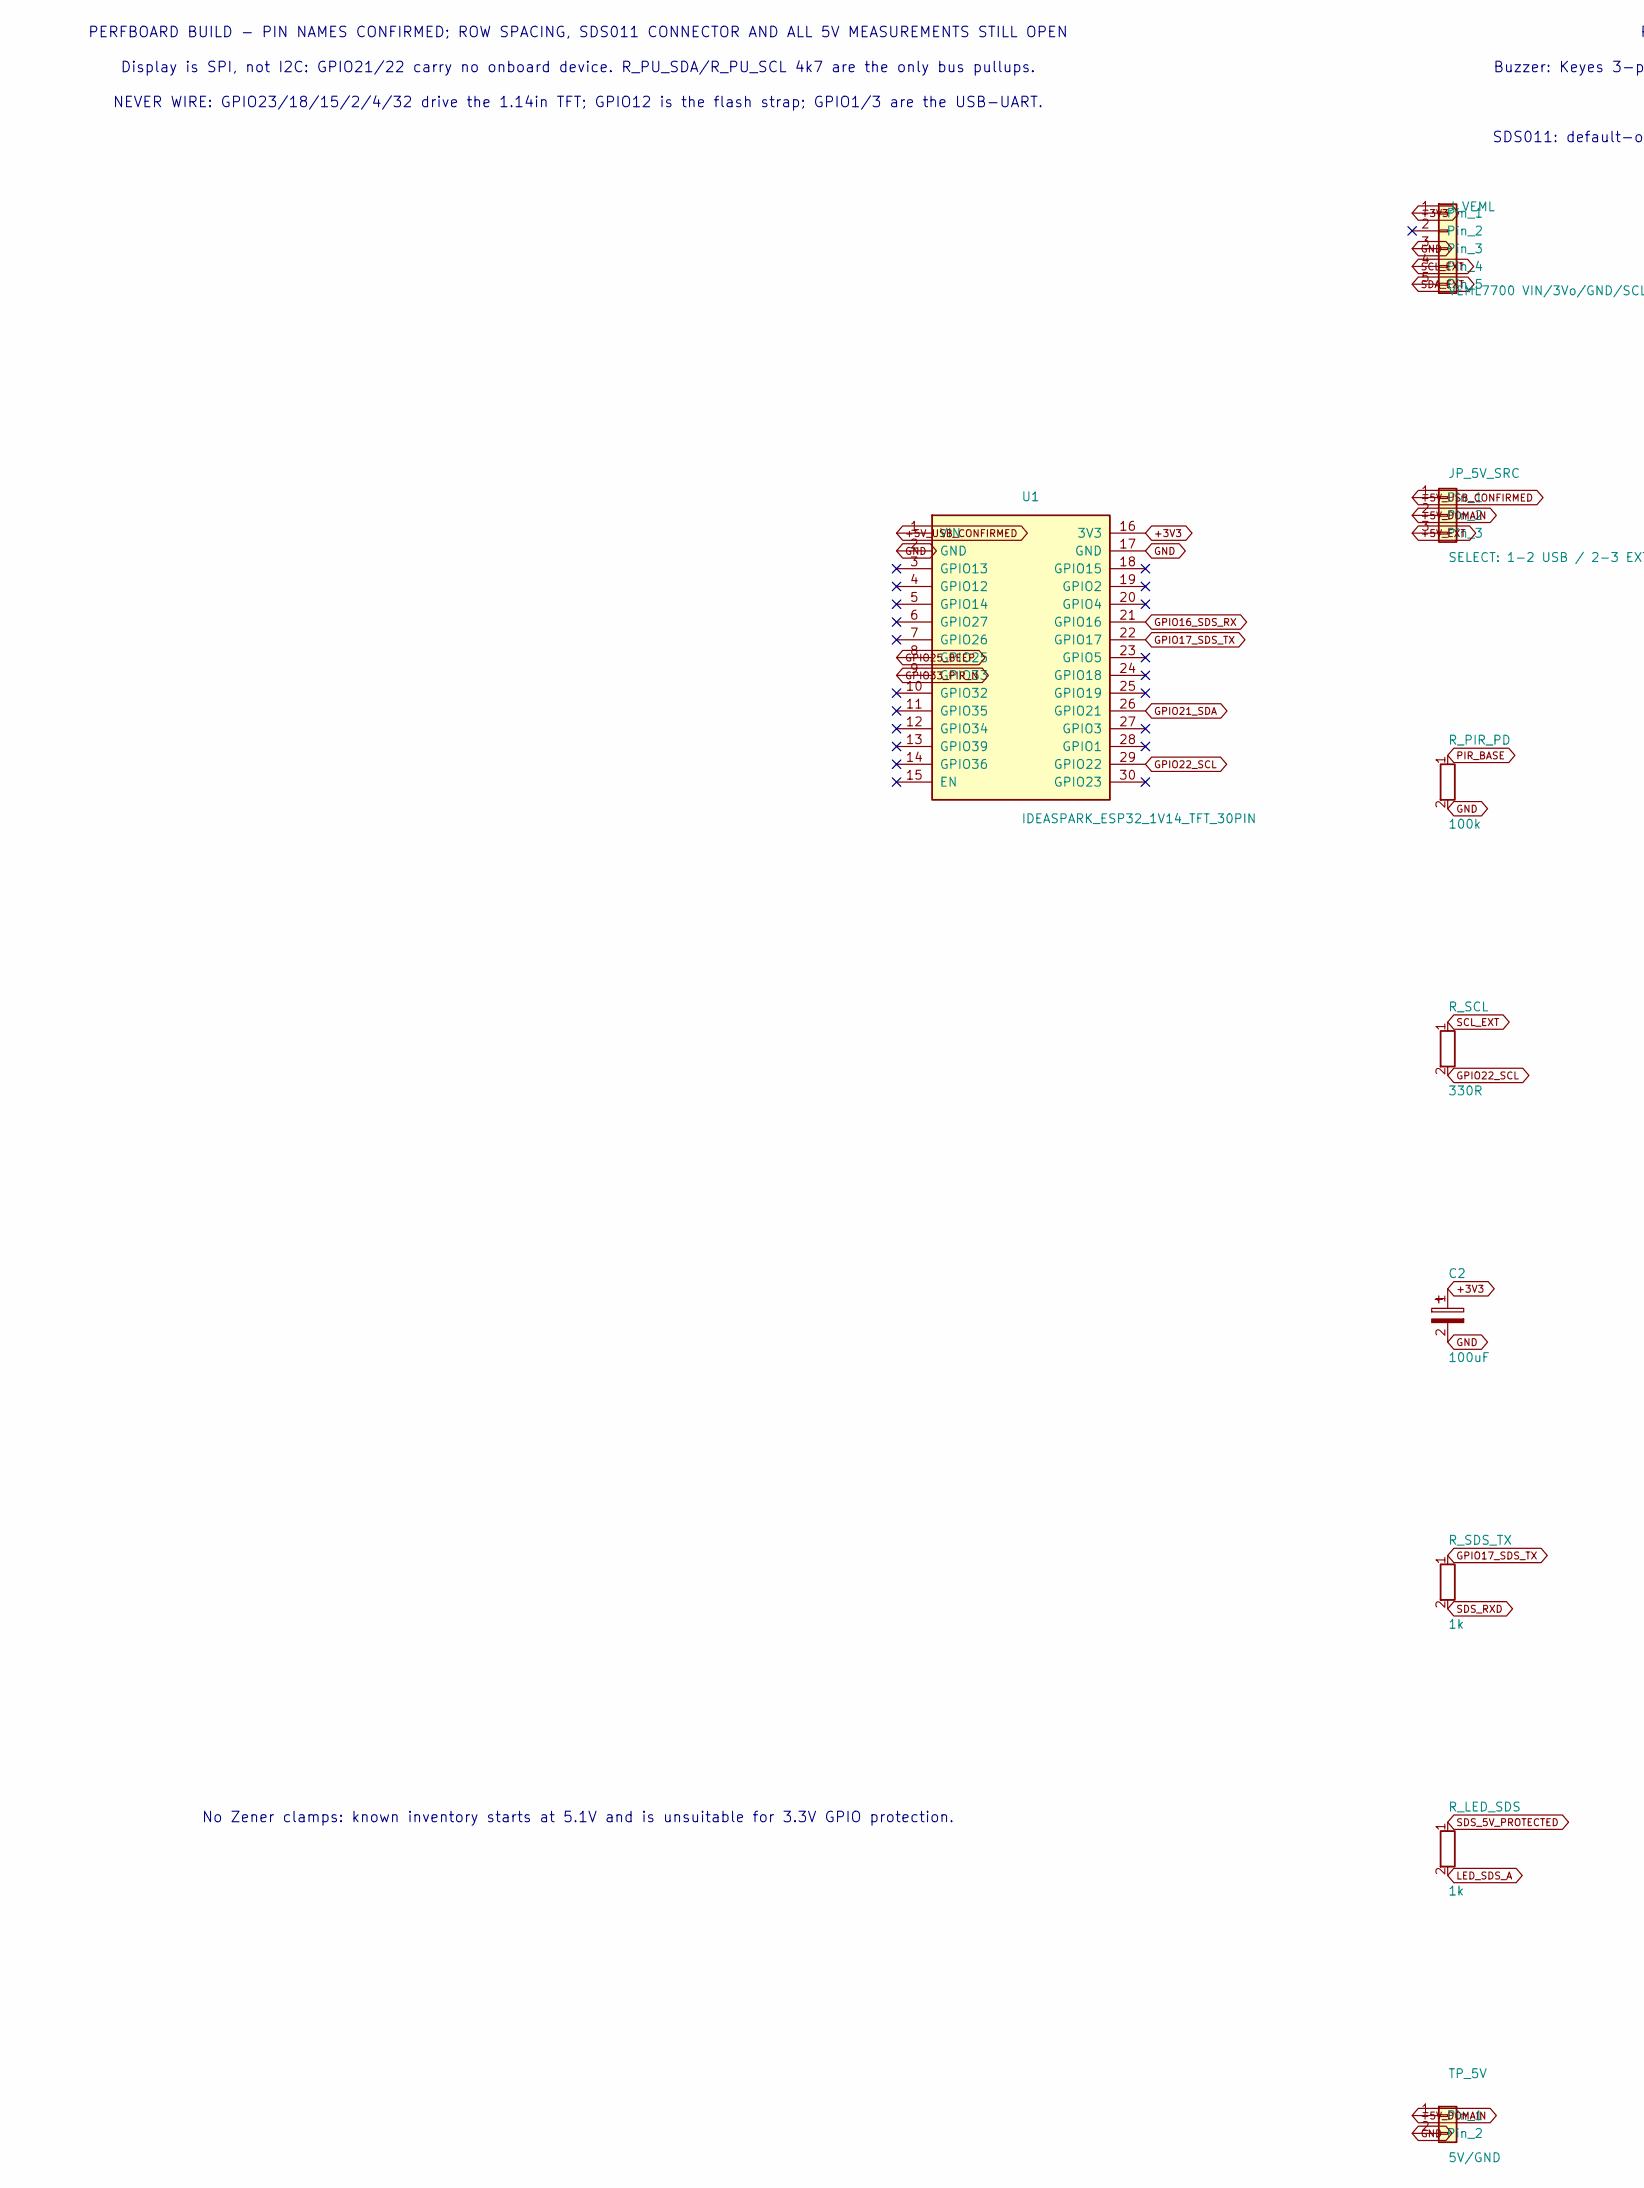
[picture p13: schematic atmosmesh-room.kicad_sch, AtmosMesh Room protected carrier, part in row 1, column 1]

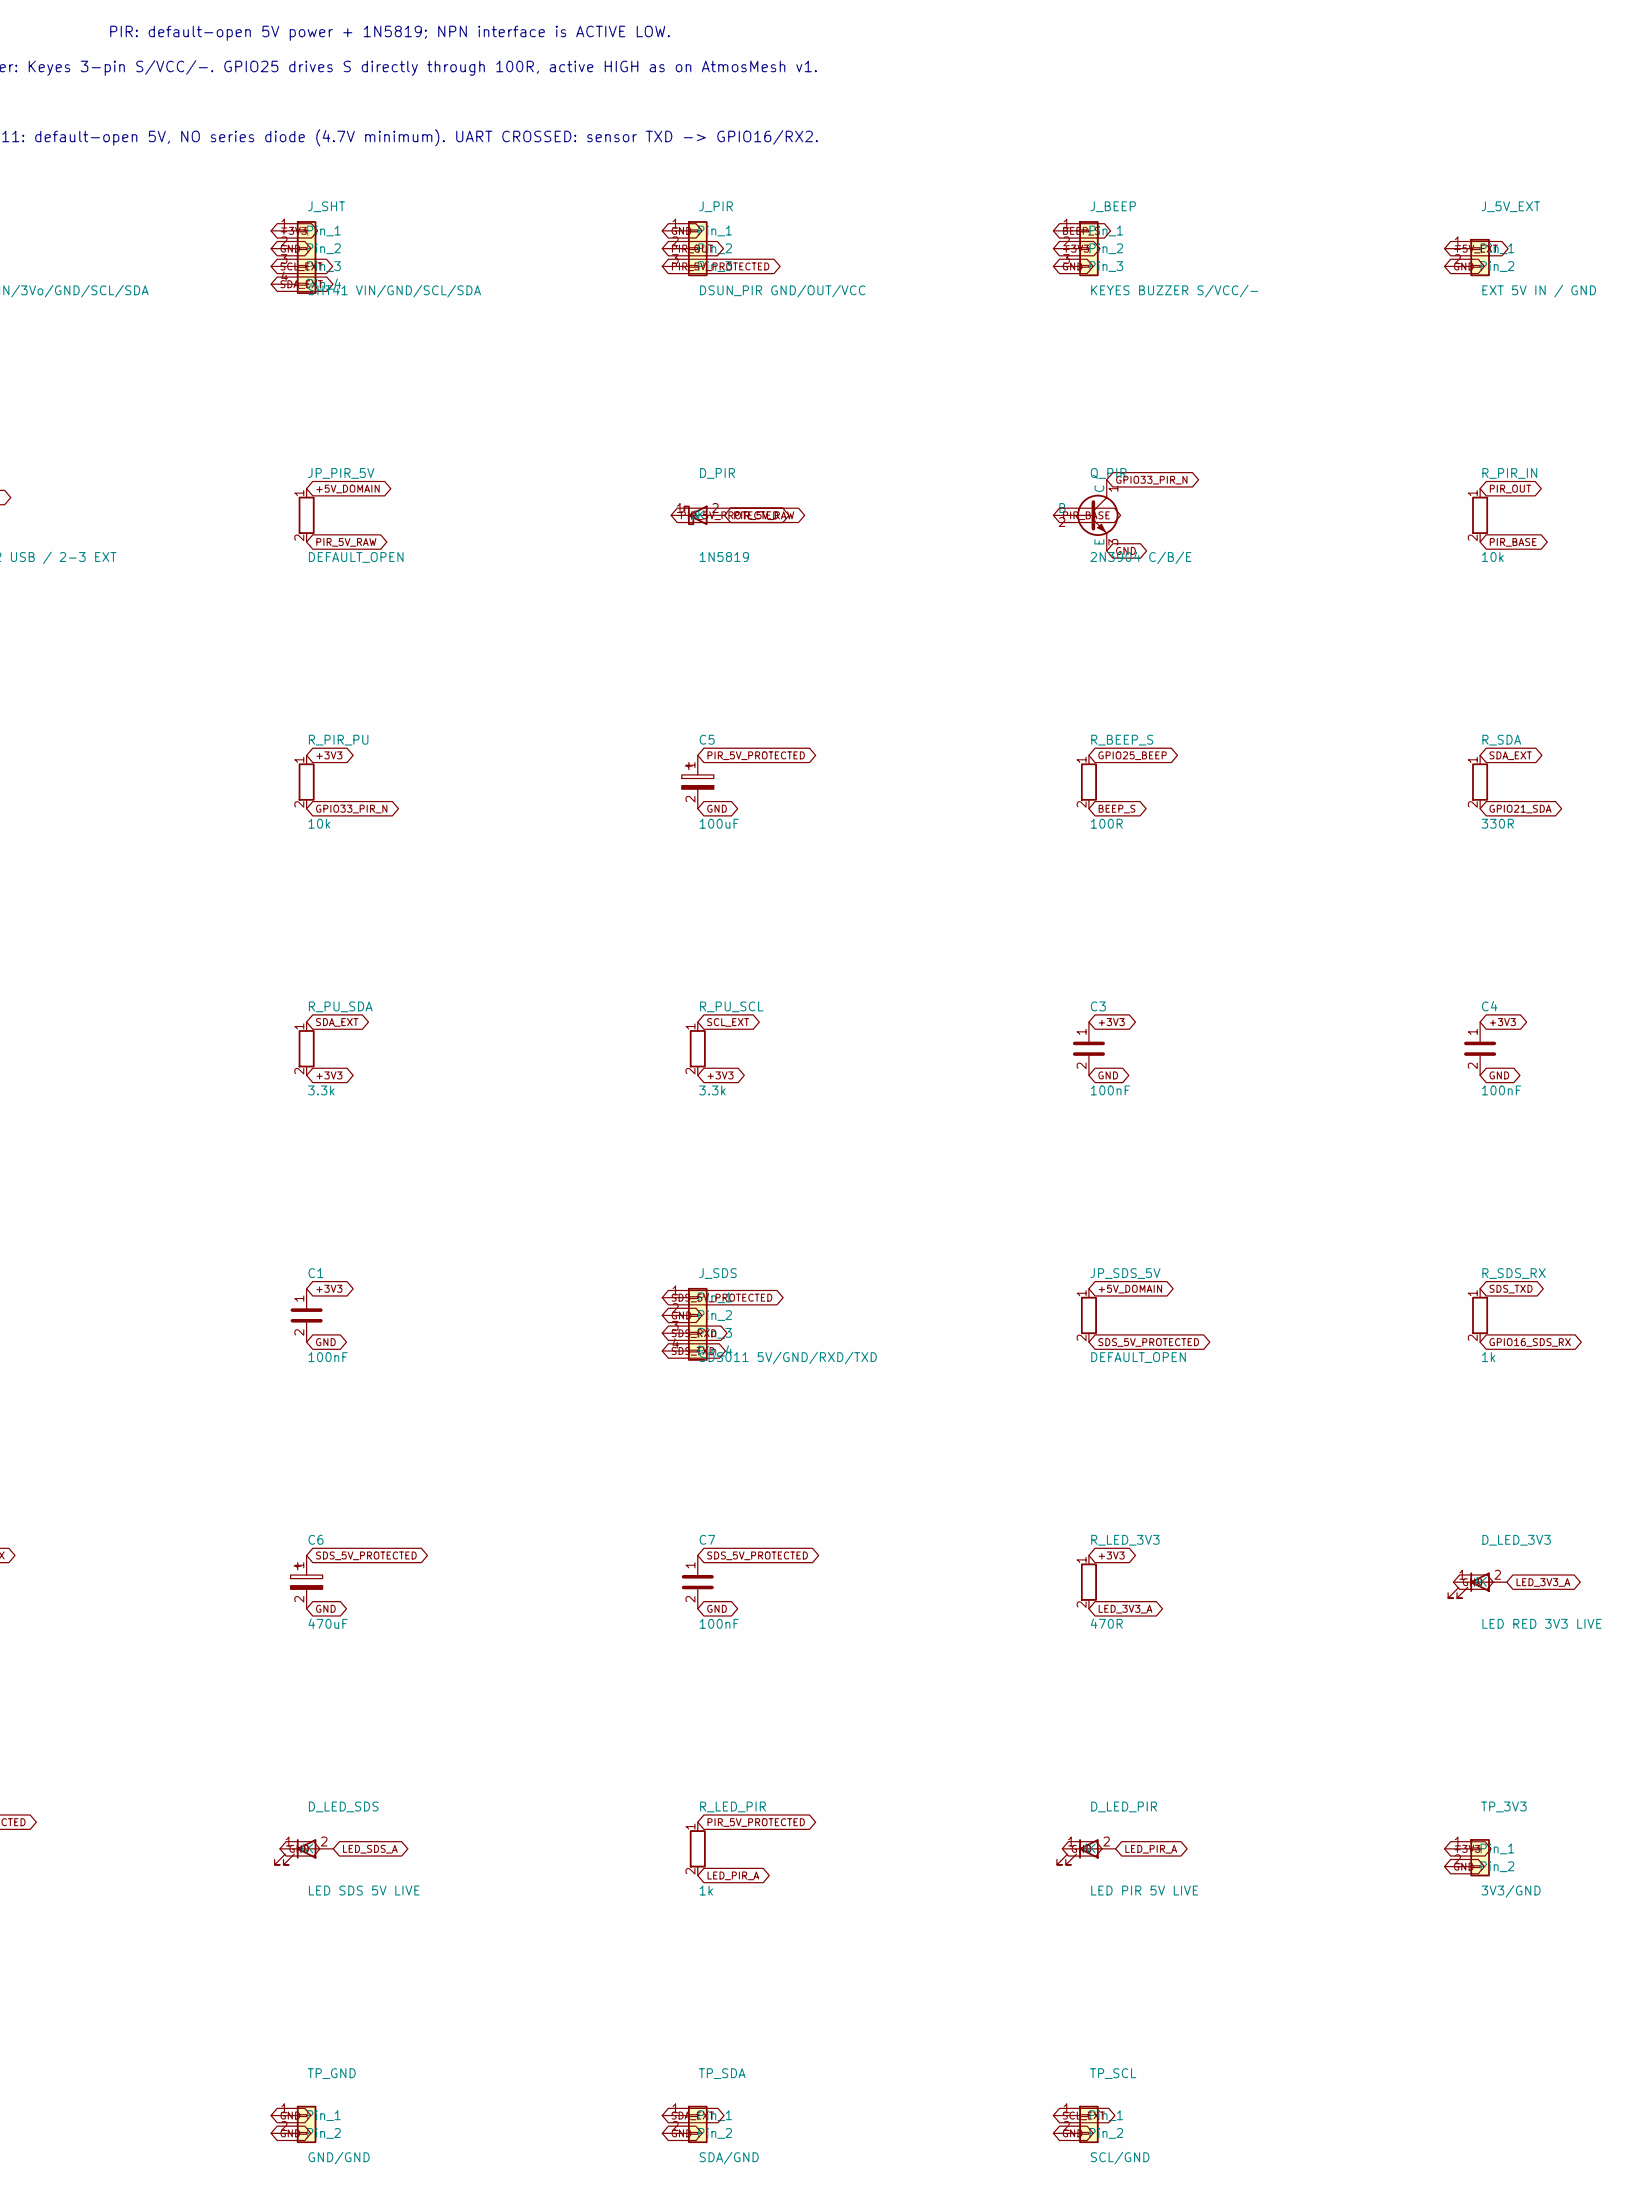
[picture p14: schematic atmosmesh-room.kicad_sch, AtmosMesh Room protected carrier, part in row 1, column 2]

Parts:
C1, C3, C4, C7: 100nF; C_Disc_P5.00mm
C2, C5: 100uF; C_Radial_P2.00mm
C6: 470uF; C_Radial_P2.00mm
D_LED_3V3: LED RED 3V3 LIVE; D_Axial_P7.62mm
D_LED_PIR: LED PIR 5V LIVE; D_Axial_P7.62mm
D_LED_SDS: LED SDS 5V LIVE; D_Axial_P7.62mm
D_PIR: 1N5819; D_Axial_P7.62mm
JP_5V_SRC: SELECT: 1-2 USB / 2-3 EXT; PinHeader_1x03_P2.54mm
JP_PIR_5V: DEFAULT_OPEN; Jumper_2_Open_P2.54mm
JP_SDS_5V: DEFAULT_OPEN; Jumper_2_Open_P2.54mm
J_5V_EXT: EXT 5V IN / GND; PinHeader_1x02_P2.54mm
J_BEEP: KEYES BUZZER S/VCC/-; PinHeader_1x03_P2.54mm
J_PIR: DSUN_PIR GND/OUT/VCC; PinHeader_1x03_P2.54mm
J_SDS: SDS011 5V/GND/RXD/TXD; PinHeader_1x04_P2.54mm
J_SHT: SHT41 VIN/GND/SCL/SDA; PinHeader_1x04_P2.54mm
J_VEML: VEML7700 VIN/3Vo/GND/SCL/SDA; PinHeader_1x05_P2.54mm
Q_PIR: 2N3904 C/B/E; TO92_CBE
R_BEEP_S: 100R; R_Axial_P7.62mm
R_LED_3V3: 470R; R_Axial_P7.62mm
R_LED_PIR: 1k; R_Axial_P7.62mm
R_LED_SDS: 1k; R_Axial_P7.62mm
R_PIR_IN: 10k; R_Axial_P7.62mm
R_PIR_PD: 100k; R_Axial_P7.62mm
R_PIR_PU: 10k; R_Axial_P7.62mm
R_PU_SCL: 3.3k; R_Axial_P7.62mm
R_PU_SDA: 3.3k; R_Axial_P7.62mm
R_SCL: 330R; R_Axial_P7.62mm
R_SDA: 330R; R_Axial_P7.62mm
R_SDS_RX: 1k; R_Axial_P7.62mm
R_SDS_TX: 1k; R_Axial_P7.62mm
TP_3V3: 3V3/GND; TestPoint_2Pin_THT
TP_5V: 5V/GND; TestPoint_2Pin_THT
TP_GND: GND/GND; TestPoint_2Pin_THT
TP_SCL: SCL/GND; TestPoint_2Pin_THT
TP_SDA: SDA/GND; TestPoint_2Pin_THT
U1: IDEASPARK_ESP32_1V14_TFT_30PIN; Ideaspark_30Pin_Provisional

Connections:
+3V3: C1.1, C2.1, C3.1, C4.1, J_BEEP.2, J_SHT.1, J_VEML.1, R_LED_3V3.1, R_PIR_PU.1, R_PU_SCL.2, R_PU_SDA.2, TP_3V3.1, U1.16 (3V3)
+5V_DOMAIN: JP_5V_SRC.2, JP_PIR_5V.1, JP_SDS_5V.1, TP_5V.1
+5V_EXT: JP_5V_SRC.3, J_5V_EXT.1
+5V_USB_CONFIRMED: JP_5V_SRC.1, U1.1 (VIN)
BEEP_S: J_BEEP.1, R_BEEP_S.2
GND: C1.2, C2.2, C3.2, C4.2, C5.2, C6.2, C7.2, D_LED_3V3.1 (K), D_LED_PIR.1 (K), D_LED_SDS.1 (K), J_5V_EXT.2, J_BEEP.3, J_PIR.1, J_SDS.2, J_SHT.2, J_VEML.3, Q_PIR.3 (E), R_PIR_PD.2, TP_3V3.2, TP_5V.2, TP_GND.1, TP_GND.2, TP_SCL.2, TP_SDA.2, U1.2 (GND), U1.17 (GND)
GPIO16_SDS_RX: R_SDS_RX.2, U1.21 (GPIO16)
GPIO17_SDS_TX: R_SDS_TX.1, U1.22 (GPIO17)
GPIO21_SDA: R_SDA.2, U1.26 (GPIO21)
GPIO22_SCL: R_SCL.2, U1.29 (GPIO22)
GPIO25_BEEP: R_BEEP_S.1, U1.8 (GPIO25)
GPIO33_PIR_N: Q_PIR.1 (C), R_PIR_PU.2, U1.9 (GPIO33)
LED_3V3_A: D_LED_3V3.2 (A), R_LED_3V3.2
LED_PIR_A: D_LED_PIR.2 (A), R_LED_PIR.2
LED_SDS_A: D_LED_SDS.2 (A), R_LED_SDS.2
PIR_5V_PROTECTED: C5.1, D_PIR.1 (K), J_PIR.3, R_LED_PIR.1
PIR_5V_RAW: D_PIR.2 (A), JP_PIR_5V.2
PIR_BASE: Q_PIR.2 (B), R_PIR_IN.2, R_PIR_PD.1
PIR_OUT: J_PIR.2, R_PIR_IN.1
SCL_EXT: J_SHT.3, J_VEML.4, R_PU_SCL.1, R_SCL.1, TP_SCL.1
SDA_EXT: J_SHT.4, J_VEML.5, R_PU_SDA.1, R_SDA.1, TP_SDA.1
SDS_5V_PROTECTED: C6.1, C7.1, JP_SDS_5V.2, J_SDS.1, R_LED_SDS.1
SDS_RXD: J_SDS.3, R_SDS_TX.2
SDS_TXD: J_SDS.4, R_SDS_RX.1

Notes on the sheet:
PERFBOARD BUILD - PIN NAMES CONFIRMED; ROW SPACING, SDS011 CONNECTOR AND ALL 5V MEASUREMENTS STILL OPEN
Display is SPI, not I2C: GPIO21/22 carry no onboard device. R_PU_SDA/R_PU_SCL 4k7 are the only bus pullups.
NEVER WIRE: GPIO23/18/15/2/4/32 drive the 1.14in TFT; GPIO12 is the flash strap; GPIO1/3 are the USB-UART.
No Zener clamps: known inventory starts at 5.1V and is unsuitable for 3.3V GPIO protection.
PIR: default-open 5V power + 1N5819; NPN interface is ACTIVE LOW.
SDS011: default-open 5V, NO series diode (4.7V minimum). UART CROSSED: sensor TXD -> GPIO16/RX2.
Buzzer: Keyes 3-pin S/VCC/-. GPIO25 drives S directly through 100R, active HIGH as on AtmosMesh v1.

Board: 2 copper layers, 44 parts (0 on the bottom side), 24 nets, no tracks yet.

Other parts of the board:
H1, H2, H3, H4: M3; MountingHole_3.2mm_M3
