konih/atmosmesh/firmware/src/products/atmosmesh_grove_v1_5.cpp

// AtmosMesh Grove v1.5 product composition root.
#include <Arduino.h>
#include <Adafruit_BMP085.h>
#include <DHT.h>
#include <U8g2lib.h>
#include <Wire.h>

#include <cmath>

#include "atmosmesh/grove_mqtt_runtime.hpp"
#include "atmosmesh/grove_visual_diagnostic.hpp"
#include "atmosmesh/grove_status.hpp"
#include "atmosmesh/product_profile.hpp"
#include "atmosmesh/rc_light.hpp"
#include "atmosmesh/soil_sampler.hpp"
#include "atmosmesh/soil_status.hpp"
#include "atmosmesh/status_led.hpp"

namespace {

constexpr unsigned long kSampleIntervalMs = 2500;
constexpr std::uint32_t kI2cClockHz = 100000;
constexpr std::uint8_t kOledAddresses[] = {0x3C, 0x3D};
constexpr std::uint8_t kBmp180Address = 0x77;

const auto& profile = atmosmesh::grove_profile();
DHT dht(profile.dht_data_gpio, DHT11);
Adafruit_BMP085 bmp180;
U8G2_SSD1306_128X32_UNIVISION_F_HW_I2C oled(U8G2_R0, U8X8_PIN_NONE,
                                             profile.i2c_scl_gpio, profile.i2c_sda_gpio);
atmosmesh::GroveReadings readings{};
atmosmesh::RcLightState light_state{};
atmosmesh::SoilSamplerState soil_state{};
bool oled_ready = false;
bool bmp_ready = false;
bool core_acquisition_attempted = false;
bool led_status_initialized = false;
atmosmesh::GroveLedStatus last_led_status = atmosmesh::GroveLedStatus::SensorFault;
atmosmesh::GroveLedReason last_led_reason = atmosmesh::GroveLedReason::CoreSensorError;
unsigned long last_sample_ms = 0;
atmosmesh::GroveVisualLedState visual_led_state{};
constexpr auto soil_calibration = atmosmesh::compiled_soil_calibration();

constexpr bool visual_diagnostic_active() {
    return atmosmesh::compiled_grove_visual_mode() ==
           atmosmesh::GroveVisualMode::OledFillAndLedCycle;
}

bool i2c_address_present(std::uint8_t address) {
    Wire.beginTransmission(address);
    return Wire.endTransmission() == 0;
}

int find_oled_address() {
    for (const auto address : kOledAddresses) {
        if (i2c_address_present(address)) {
            return address;
        }
    }
    return -1;
}

void render() {
    const auto render_action =
        atmosmesh::grove_oled_render_action(oled_ready, atmosmesh::compiled_grove_visual_mode());
    if (render_action != atmosmesh::GroveOledRenderAction::RenderLiveMeasurements) {
        return;
    }
    const auto lines = atmosmesh::grove_oled_lines(readings);
    oled.clearBuffer();
    oled.setFont(u8g2_font_5x7_tf);
    constexpr int kBaselines[] = {7, 15, 23, 31};
    for (std::size_t i = 0; i < lines.size(); ++i) {
        oled.drawStr(0, kBaselines[i], lines[i].c_str());
    }
    oled.sendBuffer();
}

void apply_light_pin_action(atmosmesh::RcLightPinAction action) {
    switch (action) {
        case atmosmesh::RcLightPinAction::DriveLow:
            pinMode(profile.light_rc_gpio, OUTPUT);
            digitalWrite(profile.light_rc_gpio, LOW);
            break;
        case atmosmesh::RcLightPinAction::ReleaseInput:
            pinMode(profile.light_rc_gpio, INPUT);
            break;
        case atmosmesh::RcLightPinAction::None:
            break;
    }
}

atmosmesh::LedPolarity led_polarity() {
    return profile.status_led_common_anode ? atmosmesh::LedPolarity::CommonAnode
                                           : atmosmesh::LedPolarity::CommonCathode;
}

void write_pin_level(int gpio, bool high) {
    digitalWrite(gpio, high ? HIGH : LOW);
}

void apply_soil_power_action(atmosmesh::SoilPowerAction action) {
    if (action != atmosmesh::SoilPowerAction::None) {
        write_pin_level(profile.soil_power_control_gpio, atmosmesh::soil_power_pin_high(action));
    }
}

void setup_soil_power_fail_safe() {
    // Set the latch HIGH before OUTPUT. The external 100k base-emitter pull-up is still mandatory
    // to hold the PNP switch off before firmware takes control.
    digitalWrite(profile.soil_power_control_gpio, HIGH);
    pinMode(profile.soil_power_control_gpio, OUTPUT);
    apply_soil_power_action(atmosmesh::soil_sampler_begin(soil_state, millis()).power_action);
}

void setup_status_led() {
    const auto off = atmosmesh::grove_led_off_levels(led_polarity());
    write_pin_level(profile.status_led_red_gpio, off.red_high);
    write_pin_level(profile.status_led_green_gpio, off.green_high);
    pinMode(profile.status_led_red_gpio, OUTPUT);
    pinMode(profile.status_led_green_gpio, OUTPUT);
}

void update_status_led(bool force = false) {
    const bool soil_acquisition_failed = atmosmesh::soil_sampler_acquisition_failed(soil_state);
    const auto soil = atmosmesh::classify_soil(
        soil_calibration, readings.soil.valid, static_cast<int>(readings.soil.raw),
        soil_acquisition_failed);
    const auto decision = atmosmesh::grove_led_decision(
        {atmosmesh::grove_core_sensors_ok(readings), core_acquisition_attempted,
         light_state.status == atmosmesh::RcLightStatus::Timeout || soil_acquisition_failed,
         atmosmesh::grove_mqtt_runtime_enabled(), atmosmesh::grove_mqtt_runtime_mqtt_up(),
         soil.condition});
    const auto levels = atmosmesh::grove_led_pin_levels(decision.status, led_polarity());
    write_pin_level(profile.status_led_red_gpio, levels.red_high);
    write_pin_level(profile.status_led_green_gpio, levels.green_high);
    if (force || !led_status_initialized || decision.status != last_led_status ||
        decision.reason != last_led_reason) {
        Serial.printf("status-led: %s reason=%s red=%s green=%s\n",
                      atmosmesh::grove_led_status_text(decision.status),
                      atmosmesh::grove_led_reason_text(decision.reason),
                      levels.red_high ? "HIGH" : "LOW",
                      levels.green_high ? "HIGH" : "LOW");
        Serial.println(atmosmesh::soil_led_status_text(decision, soil, soil_calibration).c_str());
        last_led_status = decision.status;
        last_led_reason = decision.reason;
        led_status_initialized = true;
    }
}

void apply_visual_diagnostic_led_step(const atmosmesh::GroveVisualLedStep& step) {
    if (!step.changed) {
        return;
    }
    const auto levels = atmosmesh::grove_visual_led_levels(step.phase, led_polarity());
    write_pin_level(profile.status_led_red_gpio, levels.red_high);
    write_pin_level(profile.status_led_green_gpio, levels.green_high);
    Serial.println(atmosmesh::grove_visual_led_transition_text(step.phase, levels).c_str());
}

void update_visual_diagnostic_led(unsigned long now_ms) {
    apply_visual_diagnostic_led_step(atmosmesh::grove_visual_led_tick(visual_led_state, now_ms));
}

void publish_grove_state() {
    atmosmesh::GroveMqttState state{};
    state.temperature_c = {readings.dht_temperature.value, readings.dht_temperature.valid, 0};
    state.humidity_pct = {readings.humidity.value, readings.humidity.valid, 0};
    state.pressure_hpa = {readings.pressure.value, readings.pressure.valid, 0};
    state.light_charge_us = {static_cast<float>(readings.light.charge_us), readings.light.valid, 0};
    state.soil_adc_raw = {static_cast<float>(readings.soil.raw), readings.soil.valid, 0};
    atmosmesh::grove_mqtt_runtime_publish_state(state);
}

void service_light_measurement() {
    if (!atmosmesh::rc_light_active(light_state)) {
        return;
    }
    const bool input_high = light_state.phase == atmosmesh::RcLightPhase::Charging &&
                            digitalRead(profile.light_rc_gpio) == HIGH;
    const auto now_us = micros();
    auto step = atmosmesh::rc_light_tick(light_state, now_us, input_high);
    apply_light_pin_action(step.pin_action);
    if (step.pin_action == atmosmesh::RcLightPinAction::ReleaseInput) {
        step = atmosmesh::rc_light_note_released_level(
            light_state, digitalRead(profile.light_rc_gpio) == HIGH);
    }
    if (!step.completed) {
        return;
    }
    readings.light = light_state.measurement;
    Serial.println(atmosmesh::rc_light_serial_text(light_state).c_str());
    Serial.printf("health: %s light=%s\n", atmosmesh::grove_health_text(readings).c_str(),
                  readings.light.valid ? "ok" : "unavailable");
    render();
    publish_grove_state();
}

void service_soil_measurement(unsigned long now_ms) {
    auto step = atmosmesh::soil_sampler_tick(soil_state, now_ms);
    apply_soil_power_action(step.power_action);
    if (step.sample_adc) {
        step = atmosmesh::soil_sampler_record_sample(soil_state, now_ms, analogRead(A0));
        apply_soil_power_action(step.power_action);
    }
    if (!step.completed) {
        return;
    }
    readings.soil = soil_state.measurement;
    Serial.println(atmosmesh::soil_sampler_serial_text(soil_state).c_str());
    render();
    publish_grove_state();
}

void setup_oled() {
    const int address = find_oled_address();
    if (address < 0) {
        Serial.println("oled: error not found at 0x3C/0x3D");
        if (visual_diagnostic_active()) {
            Serial.println(atmosmesh::grove_oled_fill_result_text(
                               atmosmesh::GroveOledFillResult::OledNotFound,
                               profile.oled_width_px, profile.oled_height_px)
                               .c_str());
        }
        return;
    }
    oled.setI2CAddress(static_cast<std::uint8_t>(address << 1));
    oled.setBusClock(kI2cClockHz);
    oled_ready = oled.begin();
    Serial.printf("oled: %s addr=0x%02X geometry=%dx%d\n", oled_ready ? "ok" : "error",
                  address, profile.oled_width_px, profile.oled_height_px);
    if (visual_diagnostic_active() && !oled_ready) {
        Serial.println(atmosmesh::grove_oled_fill_result_text(
                           atmosmesh::GroveOledFillResult::OledInitFailed,
                           profile.oled_width_px, profile.oled_height_px)
                           .c_str());
        return;
    }
    if (atmosmesh::grove_oled_render_action(oled_ready,
                                            atmosmesh::compiled_grove_visual_mode()) ==
        atmosmesh::GroveOledRenderAction::HoldFullAreaFill) {
        oled.clearBuffer();
        oled.setDrawColor(1);
        oled.drawBox(0, 0, profile.oled_width_px, profile.oled_height_px);
        oled.sendBuffer();
        Serial.println(atmosmesh::grove_oled_fill_result_text(
                           atmosmesh::GroveOledFillResult::Applied, profile.oled_width_px,
                           profile.oled_height_px)
                           .c_str());
    }
}

void setup_bmp180() {
    if (!i2c_address_present(kBmp180Address)) {
        Serial.println("bmp180: error not found at 0x77");
        return;
    }
    bmp_ready = bmp180.begin(BMP085_STANDARD, &Wire);
    // Keep the operator's non-default bus pins explicit even if a library calls Wire.begin().
    Wire.begin(profile.i2c_sda_gpio, profile.i2c_scl_gpio);
    Wire.setClock(kI2cClockHz);
    Serial.printf("bmp180: %s addr=0x77\n", bmp_ready ? "ok" : "error");
}

bool prepare_bmp180_sample() {
    const bool address_present = i2c_address_present(kBmp180Address);
    switch (atmosmesh::grove_bmp_action(address_present, bmp_ready)) {
        case atmosmesh::GroveBmpAction::Unavailable:
            if (bmp_ready) {
                Serial.println("bmp180: lost addr=0x77; prior reading invalidated");
            }
            bmp_ready = false;
            atmosmesh::invalidate_grove_bmp(readings);
            return false;
        case atmosmesh::GroveBmpAction::Initialize:
            bmp_ready = bmp180.begin(BMP085_STANDARD, &Wire);
            // Adafruit_BMP085 may call Wire.begin(); restore the wired D2/D3 bus explicitly.
            Wire.begin(profile.i2c_sda_gpio, profile.i2c_scl_gpio);
            Wire.setClock(kI2cClockHz);
            Serial.printf("bmp180: %s addr=0x77 after probe\n",
                          bmp_ready ? "recovered" : "initialize error");
            if (!bmp_ready) {
                atmosmesh::invalidate_grove_bmp(readings);
            }
            return bmp_ready;
        case atmosmesh::GroveBmpAction::Read:
            return true;
    }
    return false;
}

void sample_sensors() {
    const float humidity = dht.readHumidity();
    const float dht_temperature = dht.readTemperature();
    const bool dht_valid = std::isfinite(humidity) && std::isfinite(dht_temperature);
    readings.humidity = {dht_valid, dht_valid ? humidity : 0.0F};
    readings.dht_temperature = {dht_valid, dht_valid ? dht_temperature : 0.0F};

    bool bmp_valid = false;
    float bmp_temperature = 0.0F;
    float pressure_hpa = 0.0F;
    if (prepare_bmp180_sample()) {
        bmp_temperature = bmp180.readTemperature();
        pressure_hpa = bmp180.readPressure() / 100.0F;
        bmp_valid = std::isfinite(bmp_temperature) && std::isfinite(pressure_hpa) &&
                    pressure_hpa >= 300.0F && pressure_hpa <= 1100.0F;
    }
    if (bmp_valid) {
        readings.bmp_temperature = {true, bmp_temperature};
        readings.pressure = {true, pressure_hpa};
    } else {
        atmosmesh::invalidate_grove_bmp(readings);
    }

    if (dht_valid) {
        Serial.printf("dht11: ok temperature=%.1f C humidity=%.1f %%RH\n",
                      static_cast<double>(dht_temperature), static_cast<double>(humidity));
    } else {
        Serial.println("dht11: error reading unavailable");
    }
    if (bmp_valid) {
        Serial.printf("bmp180: ok temperature=%.1f C pressure=%.1f hPa\n",
                      static_cast<double>(bmp_temperature), static_cast<double>(pressure_hpa));
    } else {
        Serial.println("bmp180: error reading unavailable");
    }
    readings.light = {};
    apply_light_pin_action(atmosmesh::rc_light_begin(light_state, micros()).pin_action);
    core_acquisition_attempted = true;
}

}  // namespace

void setup() {
    setup_soil_power_fail_safe();
    setup_status_led();
    Serial.begin(115200);
    delay(200);
    Serial.printf("product=%s product_id=%s variant=%s station_id=%s\n", profile.product_name,
                  profile.product_id, profile.product_variant, profile.station_id);
    Serial.printf("i2c: SDA=D2/GPIO%d SCL=D3/GPIO%d clock=%lu Hz\n", profile.i2c_sda_gpio,
                  profile.i2c_scl_gpio, static_cast<unsigned long>(kI2cClockHz));
    Serial.println("boot-warning: D3/GPIO0 must remain HIGH during reset");
    Serial.printf("dht11: DATA=D5/GPIO%d (communication observed; values uncalibrated)\n",
                  profile.dht_data_gpio);
    Serial.printf("light: D7/GPIO%d RC raw microseconds; lower=brighter\n",
                  profile.light_rc_gpio);
    Serial.printf("status-led: red=D6/GPIO%d green=D0/GPIO%d polarity=%s "
                  "resistors=~330ohm-per-channel\n",
                  profile.status_led_red_gpio, profile.status_led_green_gpio,
                  atmosmesh::led_polarity_text(led_polarity()));
    Serial.printf("soil: control=D1/GPIO%d active=LOW interval=%lums settle=%lums samples=%u\n",
                  profile.soil_power_control_gpio,
                  static_cast<unsigned long>(atmosmesh::kSoilSampleIntervalMs),
                  static_cast<unsigned long>(atmosmesh::kSoilSettleMs),
                  static_cast<unsigned>(atmosmesh::kSoilSampleCount));
    Serial.println("soil: high-side 2N3906 PNP emitter=3V3 collector=YL-VCC "
                   "base=D1-via-2.2k pullup=100k-base-emitter");
    Serial.println("soil: AO->A0 divider=47k/15k 104-to-GND DO=unused raw-only; "
                   "onboard-divider=unknown");
    Serial.println("soil-warning: direct YL VCC->3V3 defeats firmware duty control");
    Serial.printf("soil-calibration: %s direction=%s dry=%d acceptable=%d raw-only\n",
                  atmosmesh::soil_calibration_validation_text(
                      atmosmesh::validate_soil_calibration(soil_calibration)),
                  atmosmesh::soil_direction_text(soil_calibration.direction),
                  soil_calibration.dry_cutoff_raw, soil_calibration.acceptable_cutoff_raw);
    Serial.println("power: OLED, BMP180, DHT11, LDR RC and switched YL-38 are 3V3 only");
    if (visual_diagnostic_active()) {
        Serial.println(atmosmesh::grove_visual_diagnostic_startup_banner(
                           atmosmesh::compiled_grove_visual_mode(), profile.oled_width_px,
                           profile.oled_height_px)
                           .c_str());
    }

    Wire.begin(profile.i2c_sda_gpio, profile.i2c_scl_gpio);
    Wire.setClock(kI2cClockHz);
    setup_oled();
    setup_bmp180();
    dht.begin();
    pinMode(profile.light_rc_gpio, INPUT);
    Serial.println("dht11: initialized; first read follows minimum interval");
    atmosmesh::grove_mqtt_runtime_begin();
    if (visual_diagnostic_active()) {
        apply_visual_diagnostic_led_step(
            atmosmesh::grove_visual_led_begin(visual_led_state, millis()));
    } else {
        update_status_led(true);
    }
    render();
    last_sample_ms = millis();
}

void loop() {
    const unsigned long now = millis();
    service_light_measurement();
    service_soil_measurement(now);
    if (!atmosmesh::rc_light_active(light_state) &&
        !atmosmesh::soil_sampler_power_active(soil_state) &&
        now - last_sample_ms >= kSampleIntervalMs) {
        last_sample_ms = now;
        sample_sensors();
    }
    // Defer socket work while either bounded acquisition is active. The YL power switch therefore
    // cannot remain on through a DNS/TCP/MQTT reconnect attempt.
    if (atmosmesh::grove_network_work_allowed(
            atmosmesh::rc_light_active(light_state),
            atmosmesh::soil_sampler_power_active(soil_state))) {
        atmosmesh::grove_mqtt_runtime_tick(now);
    }
    if (visual_diagnostic_active()) {
        update_visual_diagnostic_led(now);
    } else {
        update_status_led();
    }
    yield();
}
