konih/atmosmesh/firmware/test/test_native/test_product_variants.cpp

#include <cstring>
#include <string>

#include <unity.h>

#include "atmosmesh/aqua_mqtt_runtime.hpp"
#include "atmosmesh/grove_status.hpp"
#include "atmosmesh/grove_mqtt_runtime.hpp"
#include "atmosmesh/grove_visual_diagnostic.hpp"
#include "atmosmesh/product_profile.hpp"
#include "atmosmesh/rc_light.hpp"
#include "atmosmesh/soil_sampler.hpp"
#include "atmosmesh/soil_status.hpp"
#include "atmosmesh/status_led.hpp"

void test_atmosmesh_v1_profile_has_stable_identity_and_existing_pins() {
    const auto& profile = atmosmesh::atmosmesh_v1_profile();
    TEST_ASSERT_EQUAL_STRING("AtmosMesh", profile.product_name);
    TEST_ASSERT_EQUAL_STRING("atmosmesh-v1", profile.product_id);
    TEST_ASSERT_EQUAL_STRING("esp32-full-station", profile.product_variant);
    TEST_ASSERT_EQUAL_STRING("atmosmesh-0001", profile.station_id);
    TEST_ASSERT_NOT_EQUAL(0, std::strcmp(profile.product_id, profile.product_variant));
    TEST_ASSERT_NOT_EQUAL(0, std::strcmp(profile.product_id, profile.station_id));
    TEST_ASSERT_NOT_EQUAL(0, std::strcmp(profile.product_variant, profile.station_id));
    TEST_ASSERT_EQUAL_INT(5, profile.i2c_sda_gpio);
    TEST_ASSERT_EQUAL_INT(4, profile.i2c_scl_gpio);
    TEST_ASSERT_TRUE(profile.i2c_sda_is_bootstrap);
    TEST_ASSERT_FALSE(profile.i2c_scl_is_bootstrap);
    TEST_ASSERT_EQUAL_INT(18, profile.dht_data_gpio);
    TEST_ASSERT_EQUAL_INT(128, profile.oled_width_px);
    TEST_ASSERT_EQUAL_INT(64, profile.oled_height_px);
    TEST_ASSERT_EQUAL_INT(-1, profile.light_rc_gpio);
    TEST_ASSERT_EQUAL_INT(-1, profile.status_led_red_gpio);
    TEST_ASSERT_EQUAL_INT(-1, profile.status_led_green_gpio);
    TEST_ASSERT_EQUAL_INT(-1, profile.soil_power_control_gpio);
    TEST_ASSERT_EQUAL_INT(-1, profile.water_power_control_gpio);
}

void test_grove_profile_is_id_based_and_matches_wiring() {
    const auto& profile = atmosmesh::grove_profile();
    TEST_ASSERT_EQUAL_STRING("AtmosMesh Grove", profile.product_name);
    TEST_ASSERT_EQUAL_STRING("atmosmesh-grove-v1.5", profile.product_id);
    TEST_ASSERT_EQUAL_STRING("atmosmesh-v1.5", profile.product_variant);
    TEST_ASSERT_EQUAL_STRING("atmosmesh-grove-0001", profile.station_id);
    TEST_ASSERT_NOT_EQUAL(0, std::strcmp(profile.product_id, profile.product_variant));
    TEST_ASSERT_NOT_EQUAL(0, std::strcmp(profile.product_id, profile.station_id));
    TEST_ASSERT_NOT_EQUAL(0, std::strcmp(profile.product_variant, profile.station_id));
    TEST_ASSERT_EQUAL_INT(4, profile.i2c_sda_gpio);
    TEST_ASSERT_EQUAL_INT(0, profile.i2c_scl_gpio);
    TEST_ASSERT_FALSE(profile.i2c_sda_is_bootstrap);
    TEST_ASSERT_TRUE(profile.i2c_scl_is_bootstrap);
    TEST_ASSERT_EQUAL_INT(14, profile.dht_data_gpio);
    TEST_ASSERT_EQUAL_INT(128, profile.oled_width_px);
    TEST_ASSERT_EQUAL_INT(32, profile.oled_height_px);
    TEST_ASSERT_EQUAL_INT(13, profile.light_rc_gpio);
    TEST_ASSERT_EQUAL_INT(12, profile.status_led_red_gpio);
    TEST_ASSERT_EQUAL_INT(16, profile.status_led_green_gpio);
    TEST_ASSERT_EQUAL_INT(5, profile.soil_power_control_gpio);
    TEST_ASSERT_EQUAL_INT(-1, profile.water_power_control_gpio);
    TEST_ASSERT_TRUE(profile.status_led_common_anode);
}

void test_aqua_profile_is_id_based_and_uses_non_bootstrap_i2c_pins() {
    const auto& profile = atmosmesh::aqua_profile();
    TEST_ASSERT_EQUAL_STRING("AtmosMesh Aqua", profile.product_name);
    TEST_ASSERT_EQUAL_STRING("atmosmesh-aqua-v1", profile.product_id);
    TEST_ASSERT_EQUAL_STRING("esp8266-aqua-station", profile.product_variant);
    TEST_ASSERT_EQUAL_STRING("atmosmesh-aqua-0001", profile.station_id);
    TEST_ASSERT_NOT_EQUAL(0, std::strcmp(profile.product_id, profile.product_variant));
    TEST_ASSERT_NOT_EQUAL(0, std::strcmp(profile.product_id, profile.station_id));
    TEST_ASSERT_NOT_EQUAL(0, std::strcmp(profile.product_variant, profile.station_id));
    TEST_ASSERT_EQUAL_INT(4, profile.i2c_sda_gpio);
    TEST_ASSERT_EQUAL_INT(5, profile.i2c_scl_gpio);
    TEST_ASSERT_FALSE(profile.i2c_sda_is_bootstrap);
    TEST_ASSERT_FALSE(profile.i2c_scl_is_bootstrap);
    TEST_ASSERT_EQUAL_INT(-1, profile.dht_data_gpio);
    TEST_ASSERT_EQUAL_INT(128, profile.oled_width_px);
    TEST_ASSERT_EQUAL_INT(64, profile.oled_height_px);
    TEST_ASSERT_EQUAL_INT(-1, profile.light_rc_gpio);
    TEST_ASSERT_EQUAL_INT(-1, profile.status_led_red_gpio);
    TEST_ASSERT_EQUAL_INT(-1, profile.status_led_green_gpio);
    TEST_ASSERT_EQUAL_INT(-1, profile.soil_power_control_gpio);
    TEST_ASSERT_EQUAL_INT(14, profile.water_power_control_gpio);
    TEST_ASSERT_FALSE(profile.status_led_common_anode);
}

void test_grove_oled_diagnostic_policy_is_explicit_and_default_stays_live() {
    using atmosmesh::GroveVisualMode;
    using atmosmesh::GroveOledRenderAction;

    TEST_ASSERT_EQUAL(GroveVisualMode::Normal,
                      atmosmesh::compiled_grove_visual_mode());
    TEST_ASSERT_EQUAL(GroveOledRenderAction::SkipUnavailable,
                      atmosmesh::grove_oled_render_action(false,
                                                          GroveVisualMode::OledFillAndLedCycle));
    TEST_ASSERT_EQUAL(GroveOledRenderAction::RenderLiveMeasurements,
                      atmosmesh::grove_oled_render_action(true,
                                                          GroveVisualMode::Normal));
    TEST_ASSERT_EQUAL(GroveOledRenderAction::HoldFullAreaFill,
                      atmosmesh::grove_oled_render_action(true,
                                                          GroveVisualMode::OledFillAndLedCycle));
}

void test_grove_oled_full_area_banner_names_mode_and_geometry() {
    TEST_ASSERT_EQUAL_STRING(
        "visual-diagnostic: selected oled=full-area geometry=128x32 "
        "led=red-green-amber-off phase=2000ms",
        atmosmesh::grove_visual_diagnostic_startup_banner(
            atmosmesh::GroveVisualMode::OledFillAndLedCycle, 128, 32)
            .c_str());
}

void test_grove_oled_diagnostic_reports_applied_and_every_init_error_path() {
    using atmosmesh::GroveOledFillResult;
    TEST_ASSERT_EQUAL_STRING(
        "oled-diagnostic: fill applied geometry=128x32 pixels=all-on",
        atmosmesh::grove_oled_fill_result_text(GroveOledFillResult::Applied, 128, 32).c_str());
    TEST_ASSERT_EQUAL_STRING(
        "oled-diagnostic: fill not-applied geometry=128x32 reason=oled-not-found",
        atmosmesh::grove_oled_fill_result_text(GroveOledFillResult::OledNotFound, 128, 32)
            .c_str());
    TEST_ASSERT_EQUAL_STRING(
        "oled-diagnostic: fill not-applied geometry=128x32 reason=oled-init-failed",
        atmosmesh::grove_oled_fill_result_text(GroveOledFillResult::OledInitFailed, 128, 32)
            .c_str());
}

void test_grove_visual_led_sequence_uses_two_second_phases_and_repeats() {
    using atmosmesh::GroveVisualLedPhase;
    constexpr std::uint32_t started = 1000U;
    atmosmesh::GroveVisualLedState state{};
    TEST_ASSERT_EQUAL_UINT32(2000U, atmosmesh::kGroveVisualLedPhaseMs);
    auto step = atmosmesh::grove_visual_led_begin(state, started);
    TEST_ASSERT_TRUE(step.changed);
    TEST_ASSERT_EQUAL(GroveVisualLedPhase::Red, step.phase);
    step = atmosmesh::grove_visual_led_tick(state, started + 1999U);
    TEST_ASSERT_FALSE(step.changed);
    TEST_ASSERT_EQUAL(GroveVisualLedPhase::Red, step.phase);
    step = atmosmesh::grove_visual_led_tick(state, started + 2000U);
    TEST_ASSERT_TRUE(step.changed);
    TEST_ASSERT_EQUAL(GroveVisualLedPhase::Green, step.phase);
    step = atmosmesh::grove_visual_led_tick(state, started + 4000U);
    TEST_ASSERT_EQUAL(GroveVisualLedPhase::Amber, step.phase);
    step = atmosmesh::grove_visual_led_tick(state, started + 6000U);
    TEST_ASSERT_EQUAL(GroveVisualLedPhase::Off, step.phase);
    step = atmosmesh::grove_visual_led_tick(state, started + 8000U);
    TEST_ASSERT_EQUAL(GroveVisualLedPhase::Red, step.phase);

    // A late cooperative tick advances exactly one phase, so no visible phase/log is skipped.
    step = atmosmesh::grove_visual_led_tick(state, started + 20000U);
    TEST_ASSERT_TRUE(step.changed);
    TEST_ASSERT_EQUAL(GroveVisualLedPhase::Green, step.phase);
}

void test_grove_visual_led_sequence_is_wraparound_safe_and_polarity_aware() {
    using atmosmesh::GroveVisualLedPhase;
    using atmosmesh::LedPolarity;
    constexpr std::uint32_t started = 0xFFFFFF00U;
    atmosmesh::GroveVisualLedState state{};
    atmosmesh::grove_visual_led_begin(state, started);
    auto step = atmosmesh::grove_visual_led_tick(state, started + 1999U);
    TEST_ASSERT_FALSE(step.changed);
    TEST_ASSERT_EQUAL(GroveVisualLedPhase::Red, step.phase);
    step = atmosmesh::grove_visual_led_tick(state, started + 2000U);
    TEST_ASSERT_TRUE(step.changed);
    TEST_ASSERT_EQUAL(GroveVisualLedPhase::Green, step.phase);

    auto levels = atmosmesh::grove_visual_led_levels(GroveVisualLedPhase::Red,
                                                      LedPolarity::CommonCathode);
    TEST_ASSERT_TRUE(levels.red_high);
    TEST_ASSERT_FALSE(levels.green_high);
    levels = atmosmesh::grove_visual_led_levels(GroveVisualLedPhase::Green,
                                                 LedPolarity::CommonCathode);
    TEST_ASSERT_FALSE(levels.red_high);
    TEST_ASSERT_TRUE(levels.green_high);
    levels = atmosmesh::grove_visual_led_levels(GroveVisualLedPhase::Amber,
                                                 LedPolarity::CommonCathode);
    TEST_ASSERT_TRUE(levels.red_high);
    TEST_ASSERT_TRUE(levels.green_high);
    levels = atmosmesh::grove_visual_led_levels(GroveVisualLedPhase::Off,
                                                 LedPolarity::CommonCathode);
    TEST_ASSERT_FALSE(levels.red_high);
    TEST_ASSERT_FALSE(levels.green_high);

    levels = atmosmesh::grove_visual_led_levels(GroveVisualLedPhase::Red,
                                                 LedPolarity::CommonAnode);
    TEST_ASSERT_FALSE(levels.red_high);
    TEST_ASSERT_TRUE(levels.green_high);
    TEST_ASSERT_EQUAL_STRING(
        "visual-diagnostic-led: color=red D6=LOW D0=HIGH",
        atmosmesh::grove_visual_led_transition_text(GroveVisualLedPhase::Red, levels).c_str());
    levels = atmosmesh::grove_visual_led_levels(GroveVisualLedPhase::Green,
                                                 LedPolarity::CommonAnode);
    TEST_ASSERT_TRUE(levels.red_high);
    TEST_ASSERT_FALSE(levels.green_high);
    levels = atmosmesh::grove_visual_led_levels(GroveVisualLedPhase::Amber,
                                                 LedPolarity::CommonAnode);
    TEST_ASSERT_FALSE(levels.red_high);
    TEST_ASSERT_FALSE(levels.green_high);
    levels = atmosmesh::grove_visual_led_levels(GroveVisualLedPhase::Off,
                                                 LedPolarity::CommonAnode);
    TEST_ASSERT_TRUE(levels.red_high);
    TEST_ASSERT_TRUE(levels.green_high);
}

void test_grove_page_formats_valid_measurements() {
    atmosmesh::GroveReadings readings{};
    readings.dht_temperature = {true, 23.4F};
    readings.humidity = {true, 48.1F};
    readings.bmp_temperature = {true, 22.8F};
    readings.pressure = {true, 1013.2F};
    readings.light = {true, 4321U};
    readings.soil = {true, 512U};

    const auto lines = atmosmesh::grove_oled_lines(readings);
    TEST_ASSERT_EQUAL_STRING("T:23.4C RH:48%", lines[0].c_str());
    TEST_ASSERT_EQUAL_STRING("P:1013.2hPa", lines[1].c_str());
    TEST_ASSERT_EQUAL_STRING("Light:4321us", lines[2].c_str());
    TEST_ASSERT_EQUAL_STRING("Soil:512", lines[3].c_str());
    for (const auto& line : lines) {
        TEST_ASSERT_LESS_OR_EQUAL_INT(21, static_cast<int>(line.size()));
        TEST_ASSERT_EQUAL(std::string::npos, line.find("AtmosMesh"));
        TEST_ASSERT_EQUAL(std::string::npos, line.find("D1B1"));
    }
}

void test_grove_page_never_turns_missing_into_zero() {
    const auto lines = atmosmesh::grove_oled_lines({});
    TEST_ASSERT_EQUAL_STRING("T:-- RH:--", lines[0].c_str());
    TEST_ASSERT_EQUAL_STRING("P:ERR", lines[1].c_str());
    TEST_ASSERT_EQUAL_STRING("Light:--", lines[2].c_str());
    TEST_ASSERT_EQUAL_STRING("Soil:--", lines[3].c_str());
    for (const auto& line : lines) {
        TEST_ASSERT_EQUAL(std::string::npos, line.find("0"));
    }
}

void test_grove_partial_failure_is_explicit() {
    atmosmesh::GroveReadings readings{};
    readings.dht_temperature = {true, 0.0F};
    readings.humidity = {true, 0.0F};
    readings.light = {true, 0U};
    readings.soil = {true, 0U};
    const auto lines = atmosmesh::grove_oled_lines(readings);
    TEST_ASSERT_EQUAL_STRING("T:0.0C RH:0%", lines[0].c_str());
    TEST_ASSERT_EQUAL_STRING("P:ERR", lines[1].c_str());
    TEST_ASSERT_EQUAL_STRING("Light:0us", lines[2].c_str());
    TEST_ASSERT_EQUAL_STRING("Soil:0", lines[3].c_str());
    TEST_ASSERT_EQUAL_STRING("dht=ok bmp=error", atmosmesh::grove_health_text(readings).c_str());
}

void test_grove_page_names_each_missing_dht_metric_independently() {
    atmosmesh::GroveReadings readings{};
    readings.dht_temperature = {true, 25.0F};
    TEST_ASSERT_EQUAL_STRING("T:25.0C RH:--",
                             atmosmesh::grove_oled_lines(readings)[0].c_str());
    readings.dht_temperature = {};
    readings.humidity = {true, 36.0F};
    TEST_ASSERT_EQUAL_STRING("T:-- RH:36%",
                             atmosmesh::grove_oled_lines(readings)[0].c_str());
}

void test_grove_bmp_presence_rejects_cached_plausible_values_and_recovers() {
    atmosmesh::GroveReadings readings{};
    readings.bmp_temperature = {true, 22.8F};
    readings.pressure = {true, 1013.2F};

    TEST_ASSERT_EQUAL(atmosmesh::GroveBmpAction::Unavailable,
                      atmosmesh::grove_bmp_action(false, true));
    atmosmesh::invalidate_grove_bmp(readings);
    TEST_ASSERT_FALSE(readings.bmp_temperature.valid);
    TEST_ASSERT_FALSE(readings.pressure.valid);
    TEST_ASSERT_EQUAL_STRING("P:ERR", atmosmesh::grove_oled_lines(readings)[1].c_str());
    TEST_ASSERT_EQUAL(atmosmesh::GroveBmpAction::Initialize,
                      atmosmesh::grove_bmp_action(true, false));
    TEST_ASSERT_EQUAL(atmosmesh::GroveBmpAction::Read,
                      atmosmesh::grove_bmp_action(true, true));
}

void test_rc_light_policy_is_cooperative_and_reports_microseconds() {
    atmosmesh::RcLightState state{};
    auto step = atmosmesh::rc_light_begin(state, 100U);
    TEST_ASSERT_EQUAL(atmosmesh::RcLightPinAction::DriveLow, step.pin_action);
    TEST_ASSERT_FALSE(step.completed);

    step = atmosmesh::rc_light_tick(state, 100U + atmosmesh::kRcLightDischargeUs - 1U, false);
    TEST_ASSERT_EQUAL(atmosmesh::RcLightPinAction::None, step.pin_action);
    TEST_ASSERT_FALSE(step.completed);

    const std::uint32_t release_us = 100U + atmosmesh::kRcLightDischargeUs;
    step = atmosmesh::rc_light_tick(state, release_us, false);
    TEST_ASSERT_EQUAL(atmosmesh::RcLightPinAction::ReleaseInput, step.pin_action);
    TEST_ASSERT_FALSE(step.completed);

    step = atmosmesh::rc_light_tick(state, release_us + 127U, true);
    TEST_ASSERT_TRUE(step.completed);
    TEST_ASSERT_EQUAL(atmosmesh::RcLightStatus::Valid, state.status);
    TEST_ASSERT_TRUE(state.measurement.valid);
    TEST_ASSERT_EQUAL_UINT32(127U, state.measurement.charge_us);
    TEST_ASSERT_EQUAL_STRING("light: ok charge=127 us (raw; lower=brighter)",
                             atmosmesh::rc_light_serial_text(state).c_str());
}

void test_rc_light_immediate_high_is_saturated_not_zero() {
    atmosmesh::RcLightState state{};
    atmosmesh::rc_light_begin(state, 0U);
    const auto release =
        atmosmesh::rc_light_tick(state, atmosmesh::kRcLightDischargeUs, false);
    TEST_ASSERT_EQUAL(atmosmesh::RcLightPinAction::ReleaseInput, release.pin_action);
    // The hardware caller samples D7 synchronously after applying ReleaseInput. A line that is
    // already HIGH at that point is saturated even though a later loop tick cannot have elapsed=0.
    const auto step = atmosmesh::rc_light_note_released_level(state, true);
    TEST_ASSERT_TRUE(step.completed);
    TEST_ASSERT_EQUAL(atmosmesh::RcLightStatus::Saturated, state.status);
    TEST_ASSERT_FALSE(state.measurement.valid);
    TEST_ASSERT_EQUAL_UINT32(0U, state.measurement.charge_us);
    TEST_ASSERT_EQUAL_STRING("light: unavailable saturated/immediate",
                             atmosmesh::rc_light_serial_text(state).c_str());
}

void test_grove_dns_and_tcp_share_one_bounded_connect_budget() {
    TEST_ASSERT_EQUAL_UINT32(1000U, atmosmesh::kGroveMqttTransportConnectBudgetMs);
    TEST_ASSERT_EQUAL_UINT32(
        750U, atmosmesh::grove_mqtt_connect_budget_remaining_ms(1000U, 1250U));
    TEST_ASSERT_EQUAL_UINT32(
        0U, atmosmesh::grove_mqtt_connect_budget_remaining_ms(1000U, 2000U));
    TEST_ASSERT_EQUAL_UINT32(
        0U, atmosmesh::grove_mqtt_connect_budget_remaining_ms(1000U, 2500U));
    TEST_ASSERT_TRUE(atmosmesh::grove_network_work_allowed(false, false));
    TEST_ASSERT_FALSE(atmosmesh::grove_network_work_allowed(true, false));
    TEST_ASSERT_FALSE(atmosmesh::grove_network_work_allowed(false, true));
}

void test_aqua_dns_and_tcp_share_one_bounded_connect_budget() {
    TEST_ASSERT_EQUAL_UINT32(1000U, atmosmesh::kAquaMqttTransportConnectBudgetMs);
    TEST_ASSERT_EQUAL_UINT32(
        750U, atmosmesh::aqua_mqtt_connect_budget_remaining_ms(1000U, 1250U));
    TEST_ASSERT_EQUAL_UINT32(
        0U, atmosmesh::aqua_mqtt_connect_budget_remaining_ms(1000U, 2000U));
    TEST_ASSERT_EQUAL_UINT32(
        0U, atmosmesh::aqua_mqtt_connect_budget_remaining_ms(1000U, 2500U));
    TEST_ASSERT_TRUE(atmosmesh::aqua_network_work_allowed(false));
    TEST_ASSERT_FALSE(atmosmesh::aqua_network_work_allowed(true));
}

void test_rc_light_timeout_is_unavailable_and_never_zero() {
    atmosmesh::RcLightState state{};
    atmosmesh::rc_light_begin(state, 1000U);
    const std::uint32_t release_us = 1000U + atmosmesh::kRcLightDischargeUs;
    atmosmesh::rc_light_tick(state, release_us, false);
    const auto step =
        atmosmesh::rc_light_tick(state, release_us + atmosmesh::kRcLightTimeoutUs, false);
    TEST_ASSERT_TRUE(step.completed);
    TEST_ASSERT_EQUAL(atmosmesh::RcLightStatus::Timeout, state.status);
    TEST_ASSERT_FALSE(state.measurement.valid);
    TEST_ASSERT_EQUAL_UINT32(0U, state.measurement.charge_us);
    TEST_ASSERT_EQUAL_STRING("light: unavailable timeout/disconnected",
                             atmosmesh::rc_light_serial_text(state).c_str());
}

void test_rc_light_rejects_high_first_seen_after_hard_timeout() {
    atmosmesh::RcLightState state{};
    atmosmesh::rc_light_begin(state, 0U);
    const std::uint32_t release_us = atmosmesh::kRcLightDischargeUs;
    atmosmesh::rc_light_tick(state, release_us, false);
    const auto step =
        atmosmesh::rc_light_tick(state, release_us + atmosmesh::kRcLightTimeoutUs + 1U, true);
    TEST_ASSERT_TRUE(step.completed);
    TEST_ASSERT_EQUAL(atmosmesh::RcLightStatus::Timeout, state.status);
    TEST_ASSERT_FALSE(state.measurement.valid);
}

void test_grove_oled_shows_raw_light_or_explicit_missing() {
    atmosmesh::GroveReadings readings{};
    readings.light = {true, 4321U};
    readings.soil = {true, 512U};
    auto lines = atmosmesh::grove_oled_lines(readings);
    TEST_ASSERT_EQUAL_STRING("Light:4321us", lines[2].c_str());
    TEST_ASSERT_EQUAL_STRING("Soil:512", lines[3].c_str());
    readings.light = {};
    readings.soil = {};
    lines = atmosmesh::grove_oled_lines(readings);
    TEST_ASSERT_EQUAL_STRING("Light:--", lines[2].c_str());
    TEST_ASSERT_EQUAL_STRING("Soil:--", lines[3].c_str());
}

void test_soil_calibration_defaults_disabled_and_validates_both_directions() {
    using atmosmesh::SoilCalibrationValidation;
    using atmosmesh::SoilRawDirection;
    const auto compiled = atmosmesh::compiled_soil_calibration();
    TEST_ASSERT_FALSE(compiled.enabled);
    TEST_ASSERT_EQUAL(SoilRawDirection::Unknown, compiled.direction);
    TEST_ASSERT_EQUAL_INT(-1, compiled.dry_cutoff_raw);
    TEST_ASSERT_EQUAL_INT(-1, compiled.acceptable_cutoff_raw);
    TEST_ASSERT_EQUAL(SoilCalibrationValidation::Disabled,
                      atmosmesh::validate_soil_calibration(compiled));

    const atmosmesh::SoilCalibration higher{true, SoilRawDirection::HigherIsWetter, 200, 700};
    const atmosmesh::SoilCalibration lower{true, SoilRawDirection::LowerIsWetter, 800, 300};
    TEST_ASSERT_EQUAL(SoilCalibrationValidation::Valid,
                      atmosmesh::validate_soil_calibration(higher));
    TEST_ASSERT_EQUAL(SoilCalibrationValidation::Valid,
                      atmosmesh::validate_soil_calibration(lower));
}

void test_soil_calibration_rejects_unknown_range_equal_and_reversed_order() {
    using atmosmesh::SoilCalibration;
    using atmosmesh::SoilCalibrationValidation;
    using atmosmesh::SoilRawDirection;
    TEST_ASSERT_EQUAL(SoilCalibrationValidation::InvalidDirection,
                      atmosmesh::validate_soil_calibration(
                          SoilCalibration{true, SoilRawDirection::Unknown, 200, 700}));
    TEST_ASSERT_EQUAL(SoilCalibrationValidation::InvalidRange,
                      atmosmesh::validate_soil_calibration(
                          SoilCalibration{true, SoilRawDirection::HigherIsWetter, -1, 700}));
    TEST_ASSERT_EQUAL(SoilCalibrationValidation::InvalidRange,
                      atmosmesh::validate_soil_calibration(
                          SoilCalibration{true, SoilRawDirection::HigherIsWetter, 200, 1024}));
    TEST_ASSERT_EQUAL(SoilCalibrationValidation::InvalidOrder,
                      atmosmesh::validate_soil_calibration(
                          SoilCalibration{true, SoilRawDirection::HigherIsWetter, 500, 500}));
    TEST_ASSERT_EQUAL(SoilCalibrationValidation::InvalidOrder,
                      atmosmesh::validate_soil_calibration(
                          SoilCalibration{true, SoilRawDirection::HigherIsWetter, 700, 200}));
    TEST_ASSERT_EQUAL(SoilCalibrationValidation::InvalidOrder,
                      atmosmesh::validate_soil_calibration(
                          SoilCalibration{true, SoilRawDirection::LowerIsWetter, 200, 700}));
}

void test_soil_classification_is_directional_and_keeps_zero_numeric() {
    using atmosmesh::SoilCondition;
    using atmosmesh::SoilRawDirection;
    const atmosmesh::SoilCalibration higher{true, SoilRawDirection::HigherIsWetter, 200, 700};
    TEST_ASSERT_EQUAL(SoilCondition::Dry,
                      atmosmesh::classify_soil(higher, true, 0, false).condition);
    TEST_ASSERT_EQUAL(SoilCondition::Dry,
                      atmosmesh::classify_soil(higher, true, 200, false).condition);
    TEST_ASSERT_EQUAL(SoilCondition::NeedsWatering,
                      atmosmesh::classify_soil(higher, true, 201, false).condition);
    TEST_ASSERT_EQUAL(SoilCondition::Acceptable,
                      atmosmesh::classify_soil(higher, true, 700, false).condition);

    const atmosmesh::SoilCalibration lower{true, SoilRawDirection::LowerIsWetter, 800, 300};
    TEST_ASSERT_EQUAL(SoilCondition::Dry,
                      atmosmesh::classify_soil(lower, true, 1023, false).condition);
    TEST_ASSERT_EQUAL(SoilCondition::NeedsWatering,
                      atmosmesh::classify_soil(lower, true, 799, false).condition);
    TEST_ASSERT_EQUAL(SoilCondition::Acceptable,
                      atmosmesh::classify_soil(lower, true, 0, false).condition);
}

void test_soil_classification_fails_safe_before_or_without_valid_calibration() {
    using atmosmesh::SoilCondition;
    using atmosmesh::SoilRawDirection;
    const atmosmesh::SoilCalibration disabled{false, SoilRawDirection::Unknown, -1, -1};
    const atmosmesh::SoilCalibration invalid{true, SoilRawDirection::HigherIsWetter, 700, 200};
    TEST_ASSERT_EQUAL(SoilCondition::Missing,
                      atmosmesh::classify_soil(disabled, false, 0, false).condition);
    TEST_ASSERT_EQUAL(SoilCondition::Unclassified,
                      atmosmesh::classify_soil(disabled, true, 214, false).condition);
    TEST_ASSERT_EQUAL(SoilCondition::Unclassified,
                      atmosmesh::classify_soil(invalid, true, 214, false).condition);
    TEST_ASSERT_EQUAL(SoilCondition::AcquisitionFailed,
                      atmosmesh::classify_soil(disabled, false, 0, true).condition);
    TEST_ASSERT_EQUAL(SoilCondition::AcquisitionFailed,
                      atmosmesh::classify_soil(disabled, true, 2048, false).condition);
}

void test_soil_led_priority_handles_system_mqtt_and_calibrated_soil() {
    using atmosmesh::GroveLedReason;
    using atmosmesh::GroveLedStatus;
    using atmosmesh::SoilCondition;
    atmosmesh::GroveLedInputs inputs{true, true, false, false, false,
                                     SoilCondition::Acceptable};

    auto decision = atmosmesh::grove_led_decision(inputs);
    TEST_ASSERT_EQUAL(GroveLedStatus::Healthy, decision.status);
    TEST_ASSERT_EQUAL(GroveLedReason::SoilAcceptable, decision.reason);

    inputs.mqtt_configured = true;
    decision = atmosmesh::grove_led_decision(inputs);
    TEST_ASSERT_EQUAL(GroveLedStatus::SensorFault, decision.status);
    TEST_ASSERT_EQUAL(GroveLedReason::MqttConfiguredOffline, decision.reason);
    inputs.mqtt_up = true;
    inputs.soil_condition = SoilCondition::Dry;
    decision = atmosmesh::grove_led_decision(inputs);
    TEST_ASSERT_EQUAL(GroveLedStatus::SensorFault, decision.status);
    TEST_ASSERT_EQUAL(GroveLedReason::SoilDry, decision.reason);
    inputs.soil_condition = SoilCondition::NeedsWatering;
    decision = atmosmesh::grove_led_decision(inputs);
    TEST_ASSERT_EQUAL(GroveLedStatus::LocalOnly, decision.status);
    TEST_ASSERT_EQUAL(GroveLedReason::SoilNeedsWatering, decision.reason);
    inputs.soil_condition = SoilCondition::Missing;
    decision = atmosmesh::grove_led_decision(inputs);
    TEST_ASSERT_EQUAL(GroveLedStatus::LocalOnly, decision.status);
    TEST_ASSERT_EQUAL(GroveLedReason::SoilSampleMissing, decision.reason);
    inputs.soil_condition = SoilCondition::Unclassified;
    decision = atmosmesh::grove_led_decision(inputs);
    TEST_ASSERT_EQUAL(GroveLedStatus::LocalOnly, decision.status);
    TEST_ASSERT_EQUAL(GroveLedReason::SoilCalibrationNeeded, decision.reason);
    inputs.soil_condition = SoilCondition::AcquisitionFailed;
    decision = atmosmesh::grove_led_decision(inputs);
    TEST_ASSERT_EQUAL(GroveLedStatus::SensorFault, decision.status);
    TEST_ASSERT_EQUAL(GroveLedReason::AcquisitionError, decision.reason);
    inputs.soil_condition = SoilCondition::Acceptable;
    inputs.core_sensors_ok = false;
    inputs.acquisition_failed = true;
    inputs.mqtt_up = false;
    inputs.soil_condition = SoilCondition::Dry;
    decision = atmosmesh::grove_led_decision(inputs);
    TEST_ASSERT_EQUAL(GroveLedReason::CoreSensorError, decision.reason);
    inputs.core_sensors_ok = true;
    decision = atmosmesh::grove_led_decision(inputs);
    TEST_ASSERT_EQUAL(GroveLedReason::AcquisitionError, decision.reason);
}

void test_soil_led_boot_unknown_is_amber_until_core_acquisition_is_attempted() {
    using atmosmesh::GroveLedReason;
    using atmosmesh::GroveLedStatus;
    using atmosmesh::SoilCondition;
    atmosmesh::GroveLedInputs inputs{};
    inputs.core_acquisition_attempted = false;
    inputs.core_sensors_ok = false;
    inputs.soil_condition = SoilCondition::Missing;

    auto decision = atmosmesh::grove_led_decision(inputs);
    TEST_ASSERT_EQUAL(GroveLedStatus::LocalOnly, decision.status);
    TEST_ASSERT_EQUAL(GroveLedReason::SoilSampleMissing, decision.reason);

    inputs.core_acquisition_attempted = true;
    decision = atmosmesh::grove_led_decision(inputs);
    TEST_ASSERT_EQUAL(GroveLedStatus::SensorFault, decision.status);
    TEST_ASSERT_EQUAL(GroveLedReason::CoreSensorError, decision.reason);
}

void test_soil_led_serial_diagnostic_is_raw_calibration_truth() {
    using atmosmesh::SoilRawDirection;
    const atmosmesh::SoilCalibration calibration{false, SoilRawDirection::Unknown, -1, -1};
    const auto classification = atmosmesh::classify_soil(calibration, true, 214, false);
    const auto decision = atmosmesh::grove_led_decision(
        {true, true, false, false, false, classification.condition});
    TEST_ASSERT_EQUAL_STRING(
        "soil-led-status: amber reason=soil-calibration-needed raw=214 "
        "calibration=disabled direction=unknown dry=unset acceptable=unset",
        atmosmesh::soil_led_status_text(decision, classification, calibration).c_str());
}

void test_status_led_maps_health_and_polarity_deterministically() {
    using atmosmesh::GroveLedStatus;
    using atmosmesh::LedPolarity;

    auto levels = atmosmesh::grove_led_pin_levels(GroveLedStatus::SensorFault,
                                                   LedPolarity::CommonCathode);
    TEST_ASSERT_TRUE(levels.red_high);
    TEST_ASSERT_FALSE(levels.green_high);
    levels = atmosmesh::grove_led_pin_levels(GroveLedStatus::LocalOnly,
                                              LedPolarity::CommonCathode);
    TEST_ASSERT_TRUE(levels.red_high);
    TEST_ASSERT_TRUE(levels.green_high);
    levels = atmosmesh::grove_led_pin_levels(GroveLedStatus::Healthy,
                                              LedPolarity::CommonCathode);
    TEST_ASSERT_FALSE(levels.red_high);
    TEST_ASSERT_TRUE(levels.green_high);

    levels = atmosmesh::grove_led_pin_levels(GroveLedStatus::Healthy,
                                              LedPolarity::CommonAnode);
    TEST_ASSERT_TRUE(levels.red_high);
    TEST_ASSERT_FALSE(levels.green_high);
}

void test_soil_sampler_is_cooperative_bounded_and_accepts_raw_zero() {
    atmosmesh::SoilSamplerState state{};
    auto step = atmosmesh::soil_sampler_begin(state, 1000U);
    TEST_ASSERT_EQUAL(atmosmesh::SoilPowerAction::EnsureOff, step.power_action);
    TEST_ASSERT_FALSE(state.measurement.valid);
    TEST_ASSERT_FALSE(atmosmesh::soil_sampler_power_active(state));

    step = atmosmesh::soil_sampler_tick(state, 1000U + atmosmesh::kSoilSampleIntervalMs - 1U);
    TEST_ASSERT_EQUAL(atmosmesh::SoilPowerAction::None, step.power_action);
    step = atmosmesh::soil_sampler_tick(state, 1000U + atmosmesh::kSoilSampleIntervalMs);
    TEST_ASSERT_EQUAL(atmosmesh::SoilPowerAction::PowerOn, step.power_action);
    TEST_ASSERT_TRUE(atmosmesh::soil_sampler_power_active(state));

    const std::uint32_t first_sample_ms =
        1000U + atmosmesh::kSoilSampleIntervalMs + atmosmesh::kSoilSettleMs;
    step = atmosmesh::soil_sampler_tick(state, first_sample_ms - 1U);
    TEST_ASSERT_FALSE(step.sample_adc);
    for (std::uint16_t i = 0; i < atmosmesh::kSoilSampleCount; ++i) {
        const std::uint32_t sample_ms =
            first_sample_ms + i * atmosmesh::kSoilSampleSpacingMs;
        step = atmosmesh::soil_sampler_tick(state, sample_ms);
        TEST_ASSERT_TRUE(step.sample_adc);
        step = atmosmesh::soil_sampler_record_sample(state, sample_ms, 0);
    }
    TEST_ASSERT_TRUE(step.completed);
    TEST_ASSERT_EQUAL(atmosmesh::SoilPowerAction::PowerOff, step.power_action);
    TEST_ASSERT_FALSE(atmosmesh::soil_sampler_power_active(state));
    TEST_ASSERT_TRUE(state.measurement.valid);
    TEST_ASSERT_EQUAL_UINT16(0U, state.measurement.raw);
    TEST_ASSERT_EQUAL_STRING("soil: ok adc_raw=0 samples=5 power=off",
                             atmosmesh::soil_sampler_serial_text(state).c_str());
    TEST_ASSERT_EQUAL_UINT16(5U, atmosmesh::kSoilSampleCount);
    TEST_ASSERT_EQUAL_UINT32(120U, atmosmesh::kSoilNormalPowerOnMs);
    TEST_ASSERT_LESS_OR_EQUAL_UINT32(9U, atmosmesh::kSoilMaxDutyPermille);
}

void test_soil_sampler_averages_and_fails_off_at_hard_timeout() {
    atmosmesh::SoilSamplerState state{};
    atmosmesh::soil_sampler_begin(state, 0U);
    atmosmesh::soil_sampler_tick(state, atmosmesh::kSoilSampleIntervalMs);
    const std::uint32_t first = atmosmesh::kSoilSampleIntervalMs + atmosmesh::kSoilSettleMs;
    const int samples[] = {0, 100, 200, 300, 400};
    atmosmesh::SoilSamplerStep step{};
    for (std::uint16_t i = 0; i < atmosmesh::kSoilSampleCount; ++i) {
        const auto now = first + i * atmosmesh::kSoilSampleSpacingMs;
        TEST_ASSERT_TRUE(atmosmesh::soil_sampler_tick(state, now).sample_adc);
        step = atmosmesh::soil_sampler_record_sample(state, now, samples[i]);
    }
    TEST_ASSERT_TRUE(state.measurement.valid);
    TEST_ASSERT_EQUAL_UINT16(200U, state.measurement.raw);

    atmosmesh::soil_sampler_tick(state, 2U * atmosmesh::kSoilSampleIntervalMs);
    step = atmosmesh::soil_sampler_tick(
        state, 2U * atmosmesh::kSoilSampleIntervalMs + atmosmesh::kSoilMaxPowerOnMs);
    TEST_ASSERT_TRUE(step.completed);
    TEST_ASSERT_EQUAL(atmosmesh::SoilPowerAction::PowerOff, step.power_action);
    TEST_ASSERT_TRUE(atmosmesh::soil_sampler_acquisition_failed(state));
    TEST_ASSERT_FALSE(state.measurement.valid);
    TEST_ASSERT_EQUAL_STRING("soil: unavailable acquisition-timeout power=off",
                             atmosmesh::soil_sampler_serial_text(state).c_str());
    TEST_ASSERT_TRUE(atmosmesh::soil_power_pin_high(atmosmesh::SoilPowerAction::PowerOff));
    TEST_ASSERT_FALSE(atmosmesh::soil_power_pin_high(atmosmesh::SoilPowerAction::PowerOn));

    atmosmesh::soil_sampler_begin(state, 0U);
    atmosmesh::soil_sampler_tick(state, atmosmesh::kSoilSampleIntervalMs);
    TEST_ASSERT_TRUE(
        atmosmesh::soil_sampler_tick(state, first).sample_adc);
    step = atmosmesh::soil_sampler_record_sample(state, first, -1);
    TEST_ASSERT_EQUAL(atmosmesh::SoilPowerAction::PowerOff, step.power_action);
    TEST_ASSERT_TRUE(atmosmesh::soil_sampler_acquisition_failed(state));
    TEST_ASSERT_EQUAL_STRING("soil: unavailable acquisition-failed power=off",
                             atmosmesh::soil_sampler_serial_text(state).c_str());
}

void test_soil_sampler_deadlines_are_millis_wraparound_safe() {
    atmosmesh::SoilSamplerState state{};
    constexpr std::uint32_t started = 0xFFFFF000U;
    atmosmesh::soil_sampler_begin(state, started);
    const std::uint32_t due = started + atmosmesh::kSoilSampleIntervalMs;
    TEST_ASSERT_EQUAL(atmosmesh::SoilPowerAction::None,
                      atmosmesh::soil_sampler_tick(state, due - 1U).power_action);
    TEST_ASSERT_EQUAL(atmosmesh::SoilPowerAction::PowerOn,
                      atmosmesh::soil_sampler_tick(state, due).power_action);
    TEST_ASSERT_EQUAL(atmosmesh::SoilPowerAction::PowerOff,
                      atmosmesh::soil_sampler_tick(
                          state, due + atmosmesh::kSoilMaxPowerOnMs).power_action);
}

void register_product_variant_tests() {
    RUN_TEST(test_atmosmesh_v1_profile_has_stable_identity_and_existing_pins);
    RUN_TEST(test_grove_profile_is_id_based_and_matches_wiring);
    RUN_TEST(test_aqua_profile_is_id_based_and_uses_non_bootstrap_i2c_pins);
    RUN_TEST(test_grove_oled_diagnostic_policy_is_explicit_and_default_stays_live);
    RUN_TEST(test_grove_oled_full_area_banner_names_mode_and_geometry);
    RUN_TEST(test_grove_oled_diagnostic_reports_applied_and_every_init_error_path);
    RUN_TEST(test_grove_visual_led_sequence_uses_two_second_phases_and_repeats);
    RUN_TEST(test_grove_visual_led_sequence_is_wraparound_safe_and_polarity_aware);
    RUN_TEST(test_grove_page_formats_valid_measurements);
    RUN_TEST(test_grove_page_never_turns_missing_into_zero);
    RUN_TEST(test_grove_partial_failure_is_explicit);
    RUN_TEST(test_grove_page_names_each_missing_dht_metric_independently);
    RUN_TEST(test_grove_bmp_presence_rejects_cached_plausible_values_and_recovers);
    RUN_TEST(test_rc_light_policy_is_cooperative_and_reports_microseconds);
    RUN_TEST(test_rc_light_immediate_high_is_saturated_not_zero);
    RUN_TEST(test_rc_light_timeout_is_unavailable_and_never_zero);
    RUN_TEST(test_rc_light_rejects_high_first_seen_after_hard_timeout);
    RUN_TEST(test_grove_dns_and_tcp_share_one_bounded_connect_budget);
    RUN_TEST(test_aqua_dns_and_tcp_share_one_bounded_connect_budget);
    RUN_TEST(test_grove_oled_shows_raw_light_or_explicit_missing);
    RUN_TEST(test_soil_calibration_defaults_disabled_and_validates_both_directions);
    RUN_TEST(test_soil_calibration_rejects_unknown_range_equal_and_reversed_order);
    RUN_TEST(test_soil_classification_is_directional_and_keeps_zero_numeric);
    RUN_TEST(test_soil_classification_fails_safe_before_or_without_valid_calibration);
    RUN_TEST(test_soil_led_priority_handles_system_mqtt_and_calibrated_soil);
    RUN_TEST(test_soil_led_boot_unknown_is_amber_until_core_acquisition_is_attempted);
    RUN_TEST(test_soil_led_serial_diagnostic_is_raw_calibration_truth);
    RUN_TEST(test_status_led_maps_health_and_polarity_deterministically);
    RUN_TEST(test_soil_sampler_is_cooperative_bounded_and_accepts_raw_zero);
    RUN_TEST(test_soil_sampler_averages_and_fails_off_at_hard_timeout);
    RUN_TEST(test_soil_sampler_deadlines_are_millis_wraparound_safe);
}
